JoshuaSeidel/tank-monitor/boards/allinone-freenove.yaml

# ALL-IN-ONE -- Freenove ESP32-S3-WROOM (FNK0085; ESP32-S3-WROOM-1 N8R8,
# DevKitC-1 pin layout). The whole 75 gal on one board: two heaters, the fan,
# both temperature probes, TDS, pH, the floor leak sensor, lux and spectral,
# and the Chihiros light itself over BLE (packages/light_wrgb2.yaml).
# No light pod, no ADS1115, no separate light bridge, and every device on its
# own GPIOs.
#
# CUTTING OVER FROM THE OLD LIGHT BRIDGE: the lamp takes one BLE connection
# at a time. Power the aquarium-light-bridge ESP32 OFF before this board
# comes up, or the two fight for the lamp. Then turn off Home Assistant's
# "Aquarium 75 - apply light phase" automation -- this board owns the phase
# now ("Light Phase" select) and HA only reports it.
#
# Successor to boards/xiao-esp32s3-lg-dual.yaml + the light pod. Everything
# the controller did is carried over unchanged -- the tank controller, the
# dual-heater lockstep, the gradient split, tank mode, the leak alarm, the
# BLE v3 link to the panel. What changed is only where each signal enters:
#
#   - pH, TDS and leak read on the chip's own ADC1, one pin each. The
#     ADS1115 is gone because the S3 has exactly TWO I2C controllers
#     (ESPHome refuses a third bus on this chip) and both are spent on the
#     light sensors, one each.
#   - Lux and spectral are read here, directly. The pod's BLE push and the
#     controller's "rx_" globals are no longer in the path.
#
# RECALIBRATE pH and TDS after the swap, and re-check the leak thresholds:
# every analog value now comes through a different converter.
#
# ---------------------------------------------------------------------
# PIN MAP -- Freenove ESP32-S3-WROOM (labels are GPIO numbers on this board)
# ---------------------------------------------------------------------
#   signal                       GPIO   notes
#   pH board signal (blue)       1      ADC1_CH0
#   DS18B20 A (control probe)    4      4.7k pull-up to 3V3 (CAM_SIOD)
#   DS18B20 B (cross-check)      5      4.7k pull-up to 3V3 (CAM_SIOC)
#   TDS board signal             6      ADC1_CH5
#   Leak sensor                  7      ADC1_CH6; 2.2M + 100nF to GND at the pin
#   Heater A relay               8
#   Heater B relay               9
#   Fan relay                    10
#   BH1750 SDA / SCL             15 / 16   I2C bus "bus_lux"
#   AS7341 SDA / SCL             17 / 18   I2C bus "bus_spec"
#
# Left alone on purpose:
#   0, 3, 45, 46   strapping pins -- a sensor holding one at a level at
#                  reset can stop the board booting
#   35, 36, 37     the octal PSRAM
#   19, 20         native USB
#   43, 44         the USB-serial console
#   38, 39, 40     the microSD slot
#   2, 48          onboard LED and WS2812 RGB LED
# GPIO 4-18 also run to the (unfitted) camera connector; do not fit one.
# GPIO4 and GPIO5 are the camera's SCCB bus (CAM_SIOD / CAM_SIOC) and are
# PULLED UP TO 3V3 ON THE BOARD, camera or not. Never put an analog input
# on them: on 2026-09-28 TDS (GPIO4) sat at ~2.33 V in air with the probe
# unplugged, and the leak input (GPIO5) read a dead-flat 3.15 V -- "wet" --
# against its 2.2M pull-down from the first boot. The 1-Wire buses live
# there instead, because 1-Wire wants a pull-up anyway: the board's sits in
# parallel with the 4.7k.
#
# ---------------------------------------------------------------------
# POWER -- the one thing that is still shared
# ---------------------------------------------------------------------
# One 3V3 pin and one GND pin (bottom right, beside GPIO19 -- NOT the
# DevKitC-1 positions) for seven things that need 3.3 V. Splice off
# the board, as on every board in this project.
#
# The light sensors are on long leads up to the fixture, and on 2026-09-17
# a shorted BH1750 lead browned out the 3V3 rail of the board driving the
# heaters. Separate I2C buses stop a dead sensor from holding the OTHER
# sensor's lines (which is exactly what the dead BH1750 did on the pod), but
# a short on a sensor's POWER lead still pulls the whole rail down. Feed the
# two light sensors from their own small 3.3 V regulator off the 5V pin, or
# through a resettable fuse, so a sensor fault cannot brown out the heaters.
#
# WHAT THIS FILE OWES THE SHARED PACKAGES -- the board contract:
#   one_wire bus onewire_a       -> dallas_temp in packages/sensors.yaml
#   sensor id: tds_voltage       -> packages/sensors.yaml
#   sensor id: ph_voltage        -> packages/ph.yaml
#   sensor id: tank_lux          -> packages/control.yaml (illuminance)
#   output id: heater_output     -> packages/control.yaml
#   output id: fan_output        -> packages/control.yaml
#   substitution spectral_i2c    -> packages/spectral.yaml
#   substitution light_mac       -> packages/light_wrgb2.yaml
#   water_temp_b, temp_gradient, grad_ema_*  -> packages/ble_link_v3.yaml

substitutions:
  side_a_name: "A"
  side_b_name: "B"
  # Leak thresholds, volts. Carried over from the ADS1115 build; the
  # internal ADC reads the same node slightly differently, so check wet and
  # dry against "Leak Sensor Voltage" before trusting the alarm.
  leak_on_v:  "1.2"
  leak_off_v: "0.8"
  spectral_i2c: bus_spec
  # The 75's lamp -- a WRGB II Pro 120. It advertises as
  # "DYWPR120E9B8ED2E998E": the name carries its own address, so check any
  # new value against the name. Random-static; the tracker learns the type
  # from the advertisement. Read off Home Assistant's Bluetooth adapter on
  # 2026-09-29. Load-critical, so it lives here in the versioned board file
  # rather than a wrapper.
  # The CF:20:3B:6D:17:C1 this held until then is the upstream author's own
  # DYNT90, copied from the fork's example defaults -- never this tank's
  # lamp. ble_client only connects after hearing its exact address, so with
  # it the board waited silently for a lamp that is not in the house.
  light_mac: "E9:B8:ED:2E:99:8E"
  # Where the follow-the-sun light phases take sunrise and sunset from:
  # south-central Pennsylvania, rounded to ~10 km.
  light_latitude: "39.8"
  light_longitude: "-76.7"

esp32:
  board: esp32-s3-devkitc-1
  variant: esp32s3
  flash_size: 8MB
  framework:
    type: esp-idf

# MAC-based unique_ids, as on every board here: the legacy generator omits
# the device name, and same-named entities on two boards collide.
mqtt:
  discovery_unique_id_generator: mac
  # NETWORK OUTAGES MUST NOT STOP THE HEATER LOOP.
  #
  # 2026-09-30 11:01 the router went down for ~4 minutes. This board's last
  # MQTT message was 11:00:06; it rebooted at 11:02:06 on the TASK WATCHDOG
  # (uptime 185 s at 11:05:11), i.e. the main loop -- the loop that runs the
  # heaters -- stopped for over 5 s about a minute into the outage. Broker
  # restarts (TCP refused at once) never did this; a 15 s router stall on
  # 2026-10-06 did not either. The publish path that can block for 10 s is
  # closed for every board in packages/base.yaml (idf_send_async). What is
  # specific to this board is below and in the wifi block after it.
  #
  # keepalive 60 s: the default 15 s ended the session on every short
  # router stall (2026-10-06 02:49, "connection closed by client"), which
  # then re-sends every entity's discovery and state in one burst. 60 s rides
  # out a stall of under a minute; the broker marks the board offline after
  # 90 s of real silence instead of ~22. Kept to this board on purpose:
  # every other board keeps ESPHome's default, so how fast Home Assistant
  # sees them go offline is unchanged.
  keepalive: 60s

# The fallback access point (packages/base.yaml) starts after 90 s without
# Wi-Fi by default. It switches the radio to AP+STA on channel 1 and brings
# up the captive portal -- on a radio that is also holding two BLE links --
# and while the portal is up ESPHome stops scanning for the home network.
# The 2026-09-30 watchdog reset landed 60-120 s into the outage, squarely on
# that 90 s mark. Whether or not the AP start itself was the block, nothing
# good comes of it on a board bolted to a tank with known credentials: a
# router reboot is never 10 minutes, a credentials change is. Recovery by AP
# still works -- it just waits until the network is really gone. (Wi-Fi's own
# reboot_timeout, 15 min, is left alone: the AP is up from 10 to 15 min, the
# board reboots at 15 with its relays seeded off, and regulation resumes
# within seconds; the cycle repeats only while the network stays down.)
wifi:
  ap:
    ap_timeout: 10min

# Two 1-Wire buses, one probe each: a flooded probe takes down its own bus
# and nothing else, and sensors.yaml's address-less probe drops in unmodified
# (it is bound to bus A by the !extend below).
one_wire:
  - platform: gpio
    id: onewire_a
    pin: GPIO4      # control probe. 4.7k pull-up to 3V3 (+ the board's CAM_SIOD pull-up).
  - platform: gpio
    id: onewire_b
    pin: GPIO5      # cross-check probe. 4.7k pull-up to 3V3 (+ the board's CAM_SIOC pull-up).

# Two buses, one sensor each. 10 kHz on both: the leads run up to the
# fixture, and the slow clock buys capacitance margin on a long run.
i2c:
  - id: bus_lux
    sda: GPIO15
    scl: GPIO16
    frequency: 10kHz
    scan: true
  - id: bus_spec
    sda: GPIO17
    scl: GPIO18
    frequency: 10kHz
    scan: true

# Bus autopsy, run BEFORE the I2C driver claims the pins (bus priority is
# 1000; this is 1001). With the chip's own pull-ups off it asks each line:
# does a powered sensor's pull-up reach it (ext-pullup), and is it tied hard
# to 3V3 (drives-low)? Reported through "I2C Devices". List form: a mapping
# on_boot in a package can be dropped when packages merge.
esphome:
  on_boot:
    - priority: -200
      then:
        - script.execute: apply_mode
    # The per-side relays are published only from slow_pwm's
    # state_change_action, so with the tank at temperature (duty 0, no edge)
    # they sat at "unknown" indefinitely. control.yaml seeds heater_relay and
    # fan_relay the same way; slow_pwm is off at boot, so false is the truth.
    - priority: -100
      then:
        - binary_sensor.template.publish:
            id: heater_a_relay
            state: false
        - binary_sensor.template.publish:
            id: heater_b_relay
            state: false
    - priority: 1001
      then:
        - lambda: |-
            const gpio_num_t pins[4] = {GPIO_NUM_15, GPIO_NUM_16, GPIO_NUM_17, GPIO_NUM_18};
            const char *names[4] = {"lux SDA", "lux SCL", "spec SDA", "spec SCL"};
            std::string r;
            for (int i = 0; i < 4; i++) {
              gpio_config_t c{};
              c.pin_bit_mask = 1ULL << pins[i];
              c.mode = GPIO_MODE_INPUT;
              c.pull_up_en = GPIO_PULLUP_DISABLE;
              c.pull_down_en = GPIO_PULLDOWN_ENABLE;
              c.intr_type = GPIO_INTR_DISABLE;
              gpio_config(&c);
              delayMicroseconds(200);
              const int ext = gpio_get_level(pins[i]);
              c.mode = GPIO_MODE_INPUT_OUTPUT_OD;
              c.pull_up_en = GPIO_PULLUP_ENABLE;
              c.pull_down_en = GPIO_PULLDOWN_DISABLE;
              gpio_config(&c);
              gpio_set_level(pins[i], 0);
              delayMicroseconds(200);
              const int low = gpio_get_level(pins[i]);
              gpio_set_level(pins[i], 1);
              delayMicroseconds(200);
              char b[72];
              snprintf(b, sizeof(b), "%s%s ext-pullup %s, drives-low %s",
                       i ? "; " : "", names[i], ext ? "yes" : "NO", low == 0 ? "yes" : "NO");
              r += b;
            }
            id(i2c_autopsy) = r;
            ESP_LOGI("i2c", "autopsy: %s", r.c_str());

# The cross-check probe below is also the controller's veto: if the two
# probes disagree by more than the band for five minutes the heater goes
# off (control.yaml's "Probes Disagree"). Distinct from "Probe Disagreement"
# further down, which is the instantaneous gradient against its own
# threshold -- that one tells you about the tank, this one stops the heater.
tank_controller:
  cross_check: water_temp_b
  # Eight degrees, not control.yaml's two. On a 48" tank the two probes sit
  # 40" apart with a heater beside each; a real gradient of a degree or
  # two is a MEASUREMENT here (see "Temperature Gradient"), not a fault.
  # The veto exists for a probe that is lying -- the flooded DS18B20 of
  # 2026-09-14 read half the water temperature, 35 degF off -- and 8 degF
  # catches that with room to spare while never firing on the tank itself.
  # First-boot default only: the controller persists the band, and the
  # "Probe Disagreement Band" entity (raised to 15 below) changes it live.
  disagreement_band: 8.0
  # Hard high cutout raised for cycling. control.yaml's 82 degF sits above
  # anything the 70-80 slider allows but BELOW a cycling target, and the
  # setpoint is clamped to the cutout. 88 degF is still nowhere near what
  # troubles glass, silicone or a Jager; it is a backstop on the water,
  # not a limit on the target.
  max_temperature: 88.0


sensor:
  # Bind the shared package's probe to bus A, and name both probes by side.
  - id: !extend water_temp
    one_wire_id: onewire_a
  - id: !extend water_temp_f
    name: "Water Temperature ${side_a_name}"

  # ---------------------------------------------------------------
  # Analog: pH, TDS, leak -- the chip's own ADC1, one pin each
  # ---------------------------------------------------------------
  # 12 dB attenuation covers 0-~3.1 V: the TDS board swings to ~2.3 V and
  # the pH board to ~3.0 V. 16 conversions averaged per reading, then a
  # median, because the radio's transmit bursts land on the supply as
  # short spikes. Two-point calibration through this same ADC (ph.yaml's
  # capture buttons, sensors.yaml's TDS calibration) cancels its offset
  # and gain error; recalibrate both after moving to this board.
  - platform: adc
    pin: GPIO6
    id: tds_voltage
    attenuation: 12db
    samples: 16
    update_interval: 500ms
    internal: true
    filters:
      - median:
          window_size: 20
          send_every: 20
          send_first_at: 20

  - platform: adc
    pin: GPIO1
    id: ph_voltage
    attenuation: 12db
    samples: 16
    update_interval: 1s
    internal: true
    filters:
      - median:
          window_size: 10
          send_every: 5
          send_first_at: 5

  # Floor leak sensor (Level Sense LS-2600): open when dry, ~1.4 MOhm and
  # SOURCING when wet, so the input wants a pull-DOWN. At the pin:
  #   red   -> 3V3            2.2M  between GPIO7 and GND
  #   black -> GPIO7          100nF between GPIO7 and GND
  # Dry reads 0 V, wet ~1-2.5 V. The 100nF is not optional: a megohm node
  # on six feet of cable is an antenna, and it is also what gives the ADC's
  # sampling capacitor a stiff source to charge from.
  - platform: adc
    pin: GPIO7
    id: leak_voltage
    name: "Leak Sensor Voltage"
    unit_of_measurement: "V"
    accuracy_decimals: 2
    entity_category: diagnostic
    attenuation: 12db
    samples: 16
    update_interval: 2s
    filters:
      - median:
          window_size: 5
          send_every: 5
          send_first_at: 3

  # ---------------------------------------------------------------
  # Lux -- the BH1750 on its own bus, read here, no pod in the path
  # ---------------------------------------------------------------
  # sensors.yaml's BH1750 would land on an ambiguous bus (there are two), so
  # it is removed and re-declared on bus_lux as the RAW reading. tank_lux --
  # what control.yaml's thermal model consumes -- is the daylight-corrected
  # figure below, exactly as the controller computed it from the pod.
  - id: !remove tank_lux
  - platform: bh1750
    name: "Tank Light Level Raw"
    id: lux_raw
    i2c_id: bus_lux
    address: 0x23
    update_interval: 30s
    accuracy_decimals: 0
    entity_category: diagnostic
    filters:
      - filter_out: nan

  # The lamp emits essentially no near-infrared and daylight is full of it,
  # so NIR/clear (packages/spectral.yaml's sp_nir_ratio) says how much of
  # the lux is the sun. Linear unmix against the learned daylight reference
  # (cal_nir_ref, in packages/ble_link_v3.yaml): 0 NIR = all fixture, the
  # reference = all sun. Fails OPEN: no reference yet, or no spectral
  # reading, passes lux through unchanged rather than zeroing the model's
  # light term.
  - platform: template
    name: "Tank Light Level"
    id: tank_lux
    unit_of_measurement: lx
    device_class: illuminance
    state_class: measurement
    accuracy_decimals: 0
    update_interval: 30s
    lambda: |-
      const float lux = id(lux_raw).state;
      if (isnan(lux)) return {};
      const float ref = id(cal_nir_ref);
      const float nir = id(sp_nir_ratio).state;
      if (ref <= 0.0f || isnan(nir)) return lux;
      float frac = 1.0f - (nir / ref);
      if (frac < 0.0f) frac = 0.0f;
      if (frac > 1.0f) frac = 1.0f;
      return lux * frac;

  # Learn the daylight reference from every spectral reading. Fixture light
  # only ever DILUTES NIR/clear, so the running maximum is the purest
  # daylight sample there is. Only above 50 lux (in the dark both channels
  # are near zero and the ratio is noise), decaying on a ~16 day half-life so
  # it follows the seasons. Same rule the controller applied to pod frames;
  # the decay factor is scaled for one reading a minute, same as before.
  - id: !extend sp_nir_ratio
    on_value:
      then:
        - lambda: |-
            const float lux = id(lux_raw).state;
            if (isnan(x) || isnan(lux) || lux <= 50.0f) return;
            if (x > id(cal_nir_ref)) id(cal_nir_ref) = x;
            else id(cal_nir_ref) *= 0.99997f;

  # ---------------------------------------------------------------
  # Cross-check temperature probe
  # ---------------------------------------------------------------
  # NOT a second control input. packages/control.yaml regulates on
  # water_temp alone, and that is deliberate: two independent loops on one
  # body of water mislearn each other's heat as ambient bias.
  #
  # This probe exists to answer two questions the control probe cannot:
  # "is the control probe still telling the truth" and "does this tank
  # actually have a gradient".
  - platform: dallas_temp
    one_wire_id: onewire_b
    internal: true
    id: water_temp_b
    update_interval: 10s
    accuracy_decimals: 2
    filters:
      # No filter_out: nan. A stale cross-check reading is worse than none
      # -- it would keep agreeing with a control probe that has died.
      - median:
          window_size: 5
          send_every: 1
          send_first_at: 1
      # Probe B gets its OWN offset. A DS18B20 is +/-0.5 degC absolute and
      # the control loop holds +/-0.3 degF, so two uncalibrated probes can
      # read nearly a degree apart in identical water. Cross-calibrate both
      # in the same cup before trusting any gradient number below.
      - lambda: return x + id(cal_temp_offset_b_c);

  - platform: template
    name: "Water Temperature ${side_b_name}"
    unit_of_measurement: "°F"
    device_class: temperature
    state_class: measurement
    accuracy_decimals: 2
    update_interval: 30s
    lambda: |-
      if (std::isnan(id(water_temp_b).state)) return {};
      return id(water_temp_b).state * 9.0f / 5.0f + 32.0f;

  # SIGNED gradient, side A minus side B. Positive means the A half is
  # warmer. The sign is the actionable half of this number -- absolute value
  # tells you a gradient exists, the sign tells you which end to aim
  # circulation at. That matters here because the canister draws from one
  # side, so the two halves are not hydraulically equivalent even with
  # identical heat going into each.
  #
  # Log this for a week before believing in a hot spot: under ~0.3 degF
  # there is nothing to chase (and you cannot resolve less than that with
  # two DS18B20 anyway), over ~1 degF you have a circulation problem that
  # more heaters would mask rather than fix.
  - platform: template
    name: "Temperature Gradient"
    id: temp_gradient
    unit_of_measurement: "°F"
    icon: "mdi:thermometer-lines"
    state_class: measurement
    accuracy_decimals: 2
    update_interval: 30s
    lambda: |-
      const float a = id(water_temp).state;
      const float b = id(water_temp_b).state;
      if (std::isnan(a) || std::isnan(b)) return {};
      return (a - b) * 9.0f / 5.0f;

  # ---------------------------------------------------------------
  # Splitting the gradient by cause
  # ---------------------------------------------------------------
  # A gradient that appears ONLY while the heaters run is a mixing problem:
  # heat is not leaving the end it is injected at. A gradient that persists
  # while they are idle is an ambient problem: one end of the tank is losing
  # heat to a cold wall, window or floor. Those have completely different
  # fixes, and the raw gradient cannot tell them apart.
  #
  # With both elements on the same duty, the heating figure is also the
  # heater-failure detector. If one element dies or its relay stops closing,
  # its half stops receiving heat and this number walks away from zero and
  # stays there while the idle figure does not.
  - platform: template
    name: "Gradient While Heating"
    unit_of_measurement: "°F"
    icon: "mdi:thermometer-lines"
    entity_category: diagnostic
    accuracy_decimals: 2
    update_interval: 60s
    lambda: |-
      // Expire rather than publish stale. If the tank has not been in this
      // regime recently the honest answer is "unavailable", not a figure
      // from last week presented as current -- the same reasoning that
      // keeps filter_out: nan off the probe in packages/sensors.yaml.
      const uint32_t t = id(grad_heating_ms);
      if (t == 0) return {};
      if (millis() - t > 21600000UL) return {};
      if (std::isnan(id(grad_ema_heating))) return {};
      return id(grad_ema_heating);

  - platform: template
    name: "Gradient While Idle"
    unit_of_measurement: "°F"
    icon: "mdi:thermometer-lines"
    entity_category: diagnostic
    accuracy_decimals: 2
    update_interval: 60s
    lambda: |-
      const uint32_t t = id(grad_idle_ms);
      if (t == 0) return {};
      if (millis() - t > 21600000UL) return {};
      if (std::isnan(id(grad_ema_idle))) return {};
      return id(grad_ema_idle);

binary_sensor:
  # Per-element contact state. control.yaml's "Heater" is the pair; these
  # are the individual relays, and seeing them out of lockstep means a relay
  # is not following its drive.
  - platform: template
    trigger_on_initial_state: true
    id: heater_a_relay
    name: "Heater ${side_a_name}"
    device_class: running
    icon: "mdi:radiator"

  - platform: template
    trigger_on_initial_state: true
    id: heater_b_relay
    name: "Heater ${side_b_name}"
    device_class: running
    icon: "mdi:radiator"

  # Fires when the probes disagree by more than the configured band. That is
  # either a real gradient, a dead heater, or a probe drifting out of
  # calibration -- all three are things you want to be told about rather
  # than discover in the data months later.
  - platform: template
    trigger_on_initial_state: true
    name: "Probe Disagreement"
    id: probe_disagreement
    device_class: problem
    entity_category: diagnostic
    lambda: |-
      if (std::isnan(id(temp_gradient).state)) return {};
      return fabsf(id(temp_gradient).state) > id(cal_gradient_alarm_f);

  # Wet = the sensor sources into the pull-down = the voltage rises. Two
  # thresholds (substitutions above): above leak_on_v is wet, below
  # leak_off_v is dry, and in between the answer is "whatever it was" --
  # returning an empty optional leaves the state alone. That band is what
  # stops a floor that reads 0.4 V on a humid night from flickering the
  # alarm; a 0.5 V single threshold did exactly that on 2026-09-17.
  #
  # The delays are the debounce on top. A splash that bridges the tabs for
  # a few seconds is not a leak; a leak does not un-bridge them in ten.
  - platform: template
    # trigger_on_initial_state: ESPHome defaults it OFF, and then a binary
    # sensor's FIRST state fires no callbacks -- MQTT only sends a state that
    # already exists when it connects. This one's first state lands ~16 s
    # after boot (first ADC median + the 10 s delayed_off), after MQTT is up,
    # so a dry floor was never sent and HA kept the last firmware's "wet"
    # (2026-09-28). Every published template binary sensor in this repo sets
    # it, so none can go silent this way; none has on_state automations.
    trigger_on_initial_state: true
    name: "Leak"
    id: leak_floor
    device_class: moisture
    lambda: |-
      const float v = id(leak_voltage).state;
      if (std::isnan(v)) return {};
      if (v > ${leak_on_v}f) return true;
      if (v < ${leak_off_v}f) return false;
      return {};
    filters:
      - delayed_on: 5s
      - delayed_off: 10s

# ---------------------------------------------------------------
# Heaters: ONE loop, TWO relays, BOTH heating together
# ---------------------------------------------------------------
# Equal duty to both elements, simultaneously, always. NOT staged.
#
# Staging (A carries low demand alone, B joins above a threshold) delivers
# heat more smoothly in TIME -- 150W pulsing instead of 300W. That is the
# wrong trade for this tank, because it necessarily puts all the low-demand
# heat into one half. The canister draws from a single side, so flow is
# already directional; stacking a heat asymmetry on top of a flow asymmetry
# manufactures exactly the gradient the second probe exists to detect.
#
# Even injection wins. The 300W-vs-150W pulse difference is invisible
# against a thermal time constant measured in hours. The gradient it would
# create is not.
#
# packages/control.yaml takes a single `heater:` FloatOutput and its RLS
# model carries exactly one heater term (phi = [heater, fan, T-TREF, light,
# 1]). heater_output satisfies that contract and the pair behaves as one
# 300W actuator whose combined gain the model learns as a unit.
#
# The two relays stay separate rather than being ganged onto one GPIO: it
# costs a pin this board has plenty of, and it keeps the ability to cut one
# element independently if a relay welds or an element fails.
output:
  - platform: slow_pwm
    id: heater_a_pwm
    pin: GPIO8
    period: 900s
    # False is already the ESPHome default (verified in slow_pwm/output.py,
    # 2026.8.2) -- stated explicitly because it matters more here than
    # anywhere else in this repo: it keeps the two windows PHASE-LOCKED. They start together at boot and
    # are always written in the same lambda below, so equal duty means both
    # elements are energised over the same part of each window. Letting the
    # cycles restart independently would drift them apart and, at partial
    # duty, alternate the halves -- reintroducing precisely the side-to-side
    # asymmetry this design exists to avoid.
    restart_cycle_on_state_change: false
    # packages/control.yaml defines heater_relay and fan_relay but does NOT
    # publish them -- its comment says outright they are "published from
    # slow_pwm's state_change_action in the board file". Without these the
    # entities sit at the false seeded on_boot forever, and Home Assistant
    # shows a heater that never runs while the tank regulates perfectly.
    state_change_action:
      - lambda: id(heater_a_closed) = state;
      - binary_sensor.template.publish:
          id: heater_relay
          # OR, not AND: this entity answers "is heat being delivered". A
          # failed element is not its job -- Gradient While Heating covers
          # that, and the per-side sensors below show the pair in lockstep.
          state: !lambda "return id(heater_a_closed) || id(heater_b_closed);"
      - binary_sensor.template.publish:
          id: heater_a_relay
          state: !lambda "return state;"

  - platform: slow_pwm
    id: heater_b_pwm
    pin: GPIO9
    period: 900s
    restart_cycle_on_state_change: false
    state_change_action:
      - lambda: id(heater_b_closed) = state;
      - binary_sensor.template.publish:
          id: heater_relay
          state: !lambda "return id(heater_a_closed) || id(heater_b_closed);"
      - binary_sensor.template.publish:
          id: heater_b_relay
          state: !lambda "return state;"

  # NOT inverted. The D-1585TL relay outlet module is active-high -- apply
  # voltage to the control terminal and the relay closes. The cheap bare
  # boards are active-low; this is not one of those, and `inverted: true`
  # here would run every duty cycle exactly backwards.
  - platform: slow_pwm
    id: fan_output
    pin: GPIO10
    period: 900s
    restart_cycle_on_state_change: false
    state_change_action:
      - binary_sensor.template.publish:
          id: fan_relay
          state: !lambda "return state;"

  - platform: template
    id: heater_output
    type: float
    write_action:
      - lambda: |-
          const float d = clamp(state, 0.0f, 1.0f);
          // From nothing to something -- Filling released, or a call for
          // heat after coasting -- closes the relays NOW. slow_pwm decides
          // at the start of each 900 s window whether the contacts close,
          // so a demand that arrives mid-window would otherwise wait out
          // the rest of it: up to fifteen minutes of "heating" with both
          // relays open. Only this edge restarts the window. A duty that
          // merely changes mid-window keeps its place in it, because
          // restarting on every 30 s adjustment would hold the contacts
          // closed for as long as the duty kept creeping up.
          if (id(heater_demand) <= 0.0f && d > 0.0f) {
            id(heater_a_pwm).restart_cycle();
            id(heater_b_pwm).restart_cycle();
          }
          id(heater_demand) = d;
          // Same duty, same instant, both halves of the tank. If these ever
          // diverge in effect, the gradient sensors above are what tell you.
          id(heater_a_pwm).set_level(d);
          id(heater_b_pwm).set_level(d);

interval:
  # Gradient accumulation. 30s matches the probes' publish cadence; k=0.01
  # is roughly a 50 minute time constant, which is short against the tank's
  # thermal time constant of hours but long enough to reject probe noise.
  - interval: 30s
    then:
      - lambda: |-
          const float a = id(water_temp).state;
          const float b = id(water_temp_b).state;
          if (std::isnan(a) || std::isnan(b)) return;
          const float g = (a - b) * 9.0f / 5.0f;
          const float k = 0.01f;

          // Three-way, not two. "demand > 0" would bin a 2% duty cycle --
          // 18 seconds of contact per 15 minute window -- as heating, and
          // dilute the heating average with what is effectively idle data.
          // Samples in the ambiguous middle are DISCARDED rather than
          // forced into a bin they would corrupt.
          const float d = id(heater_demand);
          if (d >= 0.05f) {
            float &e = id(grad_ema_heating);
            e = std::isnan(e) ? g : (k * g + (1.0f - k) * e);
            id(grad_heating_ms) = millis();
          } else if (d <= 0.0f) {
            float &e = id(grad_ema_idle);
            e = std::isnan(e) ? g : (k * g + (1.0f - k) * e);
            id(grad_idle_ms) = millis();
          }

# ---------------------------------------------------------------
# Tank mode: Normal / Filling / Cycling
# ---------------------------------------------------------------
# Three things a new tank is, in order. The controller does the work
# (set_hold, set_setpoint_override); this is the switch on the wall.
#
#   Filling   Every output held off and nothing judged. Probes in air read
#             room temperature and disagree; a Jager out of water must not
#             be powered; the learner must not watch any of it. Releasing
#             the hold re-anchors the model and caps heat while it settles,
#             because it is new water.
#   Cycling   Regulates on "Cycling Target" instead of "Target Temperature"
#             without touching it, so the owner's number is still there when
#             the tank is done. Everything else -- fan, learning, faults --
#             runs as normal.
#   Normal    The setpoint entity, as on every other board.
select:
  - platform: template
    name: "Tank Mode"
    id: tank_mode_select
    icon: "mdi:fishbowl-outline"
    entity_category: config
    options: ["Normal", "Filling", "Cycling"]
    # Reads the global back rather than keeping its own copy -- one owner,
    # same reason the setpoint number reads the controller.
    lambda: |-
      switch (id(tank_mode)) {
        case 1: return {"Filling"};
        case 2: return {"Cycling"};
        default: return {"Normal"};
      }
    update_interval: 30s
    set_action:
      - lambda: |-
          id(tank_mode) = (x == "Filling") ? 1 : (x == "Cycling") ? 2 : 0;
      - script.execute: apply_mode

script:
  - id: apply_mode
    mode: restart
    then:
      - lambda: |-
          // A restored Filling is a Filling nobody is standing at.
          if (id(tank_mode) == 1 && millis() < 15000) id(tank_mode) = 0;
          const int m = id(tank_mode);
          id(controller).set_hold(m == 1);
          id(controller).set_setpoint_override(
              m == 2 ? (id(cycling_target_f) - 32.0f) * 5.0f / 9.0f : NAN);
          id(tank_mode_select).publish_state(m == 1 ? "Filling" : m == 2 ? "Cycling" : "Normal");

globals:
  # Result of the boot-time bus autopsy (see esphome: on_boot above).
  - id: i2c_autopsy
    type: std::string
    restore_value: false
    initial_value: '""'
  # Mirrors the demand handed to heater_output so the gradient metrics can
  # tell heating from idle. Not restored: it is a live value, and a stale
  # one after reboot would mis-bin the first sample.
  - id: heater_demand
    type: float
    restore_value: false
    initial_value: '0.0'

  # Gradient EMAs. Restored, because these are long-baseline averages and
  # throwing them away on every OTA would restart the diagnosis from zero.
  - id: grad_ema_heating
    type: float
    restore_value: true
    initial_value: 'NAN'
  - id: grad_ema_idle
    type: float
    restore_value: true
    initial_value: 'NAN'

  # Freshness stamps for the two EMAs. NOT restored: millis() restarts at
  # zero on boot, so a restored timestamp would be meaningless. Zero means
  # "no sample in this boot yet", which reads as unavailable -- honest,
  # because a restored average has no provenance in the current session.
  - id: grad_heating_ms
    type: uint32_t
    restore_value: false
    initial_value: '0'
  - id: grad_idle_ms
    type: uint32_t
    restore_value: false
    initial_value: '0'

  # Live contact state, so either relay's action can publish the pair's OR.
  - id: heater_a_closed
    type: bool
    restore_value: false
    initial_value: 'false'
  - id: heater_b_closed
    type: bool
    restore_value: false
    initial_value: 'false'

  - id: cal_temp_offset_b_c
    type: float
    restore_value: true
    initial_value: '0.0'
  - id: cal_gradient_alarm_f
    type: float
    restore_value: true
    initial_value: '1.0'

  # Cycling target, degF. 82: nitrifying bacteria double fastest in the low
  # 80s, and 82 is the top of what an empty tank's equipment shrugs at.
  - id: cycling_target_f
    type: float
    restore_value: true
    initial_value: '82.0'
  # 0 normal, 1 filling, 2 cycling. Restored, so a reboot mid-cycle stays
  # warm. Filling is NOT restored: apply_mode maps a restored 1 back to
  # normal, because a controller that reboots with its outputs held off
  # and nobody at the tank is a cold tank by morning.
  - id: tank_mode
    type: int
    restore_value: true
    initial_value: '0'

number:
  # The veto band's ceiling. control.yaml caps the entity at 5 degF, which
  # is right for a one-probe board and wrong for this one -- see the
  # disagreement_band comment on the controller above.
  - id: !extend probe_disagreement_band
    max_value: 15.0
  # Same reason as the probe's name: two offsets, two names.
  - id: !extend cal_temp_offset_num
    name: "Cal Temp Offset ${side_a_name}"

  - platform: template
    name: "Cycling Target"
    id: cycling_target_num
    icon: "mdi:bacteria-outline"
    entity_category: config
    unit_of_measurement: "°F"
    device_class: temperature
    min_value: 78.0
    max_value: 86.0
    step: 0.5
    update_interval: 60s
    lambda: "return id(cycling_target_f);"
    set_action:
      - lambda: id(cycling_target_f) = x;
      # Each of these views republishes as soon as it is set, not at the
      # next poll -- see packages/sensors.yaml.
      - component.update: cycling_target_num
      - script.execute: apply_mode

  - platform: template
    name: "Cal Temp Offset ${side_b_name}"
    id: cal_temp_offset_b_num
    icon: "mdi:thermometer-plus"
    entity_category: config
    min_value: -5.0
    max_value: 5.0
    step: 0.1
    unit_of_measurement: "°F"
    update_interval: 60s
    # Celsius on the inside like every other temperature in this project,
    # Fahrenheit on the face because that is what a human reads.
    lambda: "return id(cal_temp_offset_b_c) * 9.0f / 5.0f;"
    set_action:
      - lambda: id(cal_temp_offset_b_c) = x * 5.0f / 9.0f;
      - component.update: cal_temp_offset_b_num

  - platform: template
    name: "Gradient Alarm Threshold"
    id: cal_gradient_alarm_num
    icon: "mdi:thermometer-alert"
    entity_category: config
    min_value: 0.1
    max_value: 5.0
    step: 0.1
    unit_of_measurement: "°F"
    update_interval: 60s
    lambda: "return id(cal_gradient_alarm_f);"
    set_action:
      - lambda: id(cal_gradient_alarm_f) = x;
      - component.update: cal_gradient_alarm_num

text_sensor:
  # BUILD GUARD -- see boards/xiao-esp32s3.yaml for the incident this exists
  # because of. id(ble_tx) is defined ONLY in packages/ble_link.yaml, so
  # building this board without that file fails at compile rather than
  # producing a controller that runs the tank perfectly and advertises
  # nothing for the panel to connect to.
  - platform: template
    name: "Link Payload"
    icon: "mdi:code-string"
    entity_category: diagnostic
    update_interval: 60s
    lambda: 'return {id(ble_tx)};'

  # Which light sensor answers, on which bus, every minute -- the sensor
  # components only probe at boot and then sit at "unknown". A TIMEOUT is a
  # HUNG bus (a device or wire holding SDA/SCL), not a missing device: it is
  # reported and nothing more is sent to that bus this round, because each
  # further transaction waits out the same ~100 ms and a sweep of them would
  # trip the task watchdog. On "no ack" the bus is swept, so a sensor at the
  # wrong address shows up where it is. The boot autopsy is appended on any
  # failure.
  - platform: template
    name: "I2C Devices"
    id: i2c_devices
    icon: "mdi:transit-connection-variant"
    entity_category: diagnostic
    update_interval: 60s
    lambda: |-
      std::string out;
      bool any_bad = false;
      auto check = [&](i2c::I2CBus *bus, uint8_t addr, const char *label) {
        App.feed_wdt();
        const auto err = bus->write_readv(addr, nullptr, 0, nullptr, 0);
        if (!out.empty()) out += ", ";
        out += label;
        if (err == i2c::ERROR_OK) { out += " ok"; return; }
        any_bad = true;
        if (err == i2c::ERROR_TIMEOUT) { out += " BUS STUCK"; return; }
        out += (err == i2c::ERROR_NOT_ACKNOWLEDGED) ? " no ack" : " error";
        std::string found;
        for (uint8_t a = 0x08; a < 0x78; a++) {
          App.feed_wdt();
          const auto e = bus->write_readv(a, nullptr, 0, nullptr, 0);
          if (e == i2c::ERROR_TIMEOUT) { found += " (hung mid-sweep)"; break; }
          if (e != i2c::ERROR_OK) continue;
          char b[8];
          snprintf(b, sizeof(b), " 0x%02X", a);
          found += b;
        }
        out += found.empty() ? " (bus empty)" : " (bus has" + found + ")";
      };
      check(id(bus_lux), 0x23, "BH1750");
      check(id(bus_spec), 0x39, "AS7341");
      if (any_bad && !id(i2c_autopsy).empty()) out += "; at boot: " + id(i2c_autopsy);
      return out;

  # WHY IT LAST CRASHED -- kept across the reboot and across power cuts
  # (components/crash_report). "Reset Reason" says only "task watchdog";
  # these say where. "Last Crash" is the reason, the core, and for a
  # watchdog the unit of work the main loop was stuck in and for how long,
  # e.g. "Task wdt on core 0; main loop stuck 5.0 s in 'mqtt' ...".
  # "Last Crash Backtrace" is the PC and backtrace; decode against the
  # firmware.elf of the build that crashed:
  #   xtensa-esp32s3-elf-addr2line -pfiaC -e .esphome/build/<name>/build/<name>.elf 0x... 0x...
  # Both read "none recorded" until there is something to record.
  - platform: template
    name: "Last Crash"
    icon: "mdi:alert-octagon-outline"
    entity_category: diagnostic
    update_interval: 60s
    lambda: 'return {id(crash).summary()};'
  - platform: template
    name: "Last Crash Backtrace"
    icon: "mdi:format-list-numbered"
    entity_category: diagnostic
    update_interval: 60s
    lambda: 'return {id(crash).backtrace()};'

button:
  # Once a crash has been read and dealt with, so the next one is not
  # confused with it.
  - platform: template
    name: "Clear Crash Report"
    icon: "mdi:delete-sweep-outline"
    entity_category: config
    on_press:
      - lambda: id(crash).clear();

# The crash record itself: ESPHome's panic backtrace plus a task-watchdog
# breadcrumb, captured at boot and saved to flash. See the text sensors above.
external_components:
  - source:
      type: git
      url: https://github.com/JoshuaSeidel/tank-monitor
      ref: main
    components: [crash_report]
    refresh: 0s

crash_report:
  id: crash

# The AS7341 and its derived values (shares, NIR ratio, saturation), shared
# with the light pod. Included from HERE so this board file alone is a
# complete build: a wrapper cannot leave the spectral side out.
packages:
  spectral: !include ../packages/spectral.yaml
  # The lamp, held over BLE, with the phase table and lux-based detection on
  # this chip. Needs tank_lux above (lamp-only lux) and the esp32_ble block
  # from ble_link_v3.yaml. Included here for the same reason: a wrapper
  # cannot leave it out.
  light: !include ../packages/light_wrgb2.yaml
