JoshuaSeidel/tank-monitor/packages/light_wrgb2.yaml

# The tank light, driven from the tank's own board.
#
# A Chihiros WRGB II / WRGB II Pro, controlled over BLE from the same chip
# that runs the heaters, using the protocol helpers in the
# JoshuaSeidel/chihiros-esphome fork. This replaces the separate
# aquarium-light-bridge ESP32 AND the Home Assistant automation that used to
# re-push the schedule every half hour. Everything here runs on the board:
# Home Assistant only reports it, exactly as it does for the heaters.
#
# TUNING NEEDS NO FLASH. The phase table is stored in flash memory, not
# compiled in: "Light White/Red/Green/Blue/Ramp/On Time/Off Time" edit the
# selected phase, save it, and push it within a couple of seconds. The
# numbers in light_seed_defaults are first-boot defaults and what "Reset
# Light Phase to Defaults" restores -- nothing else.
#
# Needs from the including build:
#   ${light_mac}      the lamp's BLE MAC (the board file sets it)
#   sensor tank_lux   LAMP-ONLY lux -- daylight already unmixed out by NIR
#   global cal_nir_ref  the learned daylight reference (ble_link_v3.yaml)
#   time sntp_time    packages/base.yaml
#   esp32_ble         packages/ble_link_v3.yaml (the panel server)
#   ble_guard         packages/ble_link_v3.yaml (disconnect reasons)
#
# ---------------------------------------------------------------------
# WHY THE LINK IS HELD OPEN
# ---------------------------------------------------------------------
# The upstream bridge connects, pushes, and disconnects, and scans
# continuously so it can reconnect at any moment. On a board that also runs
# the heaters and serves the panel, a scanner that never stops is radio time
# taken from Wi-Fi and the panel link for no reason. Here the tracker scans
# from boot only until the lamp connects, then stops; it scans again only if
# the link drops. With both links up, the radio does not scan at all.
#
# Held open, the link also means the Chihiros app CANNOT connect -- the lamp
# takes one connection at a time. That is the point: nothing overrides the
# phase selected here. "Release Light for App" hands the lamp over for 30
# minutes and then takes it back, re-pushing the selected phase, so whatever
# was done in the app is undone automatically. A release cannot be left on.
#
# ---------------------------------------------------------------------
# DETECTION -- "the schedule says lit and the lamp is dark"
# ---------------------------------------------------------------------
# The lamp cannot report its state, so this looks at it instead. tank_lux is
# lamp-only light (daylight is removed by its near-infrared signature, see
# the board file), so it answers "is the fixture actually on" even with the
# window open. Room LEDs have no NIR either and DO leak into it, which is why
# the lit level is LEARNED rather than guessed -- a guessed lux threshold was
# wrong on this project for a year once already:
#
#   * During the plateau of a lit phase, while the reading looks lit, the
#     plateau lux is tracked as an average ("Light Learned Lux").
#   * Plateau and reading below max(20 lx, a quarter of the learned level)
#     for 5 minutes = the lamp is dark when it should be lit. Re-push.
#   * Well outside the photoperiod and reading above HALF the learned level
#     for 5 minutes = lit when it should be dark (lights left on overnight is
#     the algae case). Re-push. Disabled until BOTH a lit level and the
#     daylight reference (cal_nir_ref) have been learned: tank_lux passes
#     sunlight through as lamp light until then, so a fresh board on a sunny
#     afternoon would otherwise "detect" a lamp that is actually off.
#   * No more than one fix per 15 minutes; after 3 fixes that did not take,
#     stop pushing and raise "Light Not Responding" rather than hammering the
#     radio. It clears the moment the lamp matches again.
#
# Ramps are excluded (5 min margin each side on top of the ramp itself) --
# mid-ramp the lux is legitimately anywhere. Assumes the photoperiod does
# not cross midnight; none of the phases do.

substitutions:
  # The Nordic UART service every Chihiros device speaks. Fixed by the
  # lamp, not a setting. The panel server in ble_link_v3.yaml advertises the
  # same service UUID -- no clash: that is the board's own GATT server, this
  # is a client connection to a different device.
  light_ble_service: "6e400001-b5a3-f393-e0a9-e50e24dcca9e"
  light_ble_tx:      "6e400002-b5a3-f393-e0a9-e50e24dcca9e"
  light_ble_rx:      "6e400003-b5a3-f393-e0a9-e50e24dcca9e"
  # "true" for a WRGB II Pro (independent white channel).
  light_pro: "true"

external_components:
  - source:
      type: git
      url: https://github.com/JoshuaSeidel/chihiros-esphome
      ref: main
    components: [chihiros_ble]
    # The default 1d would silently build yesterday's protocol code.
    refresh: 0s

# Pulls in the protocol headers (frame builder, WRGB2Device). No options.
chihiros_ble:

# Scans from boot until the lamp is found; the ble_client's on_connect stops
# it. Same timing the upstream bridge uses; active, because the lamp's name
# rides in the scan response.
esp32_ble_tracker:
  scan_parameters:
    active: true
    interval: 320ms
    window: 60ms
    continuous: true

ble_client:
  - mac_address: ${light_mac}
    id: light_ble
    on_connect:
      then:
        - lambda: |-
            id(light_linked) = true;
            id(light_up_ms) = millis();
        - esp32_ble_tracker.stop_scan:
        - logger.log:
            level: INFO
            format: "light: linked, scanning stopped"
        # Always re-push on (re)connect: whatever happened while the link was
        # down -- a reboot, a release to the app -- is overwritten here.
        - delay: 500ms
        - script.execute: light_push
    # Fires on ESP_GATTC_CLOSE_EVT only. ESPHome has two ways to end a link
    # WITHOUT that event: its 10 s "Timeout waiting for CLOSE_EVT, forcing
    # IDLE" path in BLEClientBase::loop(), and a BLE stack teardown. Either
    # one left Light Linked stuck on and the scan never restarted -- the
    # watchdog interval below is what catches those.
    on_disconnect:
      then:
        - script.execute:
            id: light_link_down
            cause: 1

globals:
  - id: light_device
    type: chihiros::WRGB2Device
    restore_value: false
  - id: light_linked
    type: bool
    restore_value: false
    initial_value: 'false'
  - id: light_released
    type: bool
    restore_value: false
    initial_value: 'false'
  # Link diagnostics. Not restored: they describe this boot's link, and
  # millis() stamps mean nothing after a reboot. "Light Link Drops" is
  # total_increasing, so Home Assistant handles the reset to 0.
  #   light_down_cause  0 none yet, 1 disconnect event, 2 found by watchdog
  - id: light_link_drops
    type: uint32_t
    restore_value: false
    initial_value: '0'
  - id: light_up_ms
    type: uint32_t
    restore_value: false
    initial_value: '0'
  - id: light_down_cause
    type: int
    restore_value: false
    initial_value: '0'
  # Consecutive 10 s watchdog checks that disagreed with the real client
  # state / found the scan not running. Two in a row before acting, so a
  # transition caught mid-flight is not "corrected".
  - id: light_wd_strikes
    type: int
    restore_value: false
    initial_value: '0'
  - id: light_scan_strikes
    type: int
    restore_value: false
    initial_value: '0'
  # The selected phase, resolved from the table in light_select_phase.
  # Detection compares the lamp against THIS, not against what was last
  # successfully pushed.
  - id: lp_valid
    type: bool
    restore_value: false
    initial_value: 'false'
  - id: lp_auto
    type: bool
    restore_value: false
    initial_value: 'false'
  - id: lp_on_min
    type: int
    restore_value: false
    initial_value: '540'
  - id: lp_off_min
    type: int
    restore_value: false
    initial_value: '840'
  - id: lp_ramp
    type: int
    restore_value: false
    initial_value: '30'
  - id: lp_r
    type: int
    restore_value: false
    initial_value: '0'
  - id: lp_g
    type: int
    restore_value: false
    initial_value: '0'
  - id: lp_b
    type: int
    restore_value: false
    initial_value: '0'
  - id: lp_w
    type: int
    restore_value: false
    initial_value: '0'
  # Learned plateau lux. Persisted: a reboot should not forget what "on"
  # looks like. Zeroed on a phase change, because the new phase is a
  # different brightness.
  - id: light_learned_lux
    type: float
    restore_value: true
    initial_value: '0.0'
  - id: light_mismatch_min
    type: int
    restore_value: false
    initial_value: '0'
  - id: light_fix_attempts
    type: int
    restore_value: false
    initial_value: '0'
  - id: light_last_fix_ms
    type: uint32_t
    restore_value: false
    initial_value: '0'
  - id: light_not_responding
    type: bool
    restore_value: false
    initial_value: 'false'
  # 0 unknown, 1 off phase, 2 dark (outside the photoperiod), 3 ramping,
  # 4 lit (plateau). Drives detection and "Light Expected".
  - id: light_expected
    type: int
    restore_value: false
    initial_value: '0'
  # THE PHASE TABLE, stored in flash so it is tuned from Home Assistant or the
  # board's own page and survives reboots and reflashes -- changing a
  # brightness never needs a build. Five phases x seven fields, in select
  # order: [on_min, off_min, ramp, W, R, G, B]. Zero until first boot seeds
  # it from light_seed_defaults, which is the ONLY place default values are
  # written down.
  - id: light_table
    type: std::array<int, 35>
    restore_value: true
  - id: light_table_seeded
    type: bool
    restore_value: true
    initial_value: 'false'
  # FOLLOW THE SUN, per phase, in select order. 0 = the table's fixed times.
  # >0 = the lights span today's sunrise to sunset and this many minutes of
  # it are full brightness; the rest of the natural day is a slow dawn and
  # dusk ramp. Kept apart from light_table so adding it did not discard the
  # stored table. Seeded by light_seed_sun, the only place its defaults live.
  - id: light_sun_plateau
    type: std::array<int, 5>
    restore_value: true
  - id: light_sun_seeded
    type: bool
    restore_value: true
    initial_value: 'false'
  # The selected phase follows the sun: lp_on/off/ramp are computed, not
  # read from the table. lp_sun_day is the day of year they were computed
  # for (-1 = not yet), so the minute tick recomputes after midnight and
  # once the clock first syncs.
  - id: lp_sun
    type: bool
    restore_value: false
    initial_value: 'false'
  - id: lp_sun_day
    type: int
    restore_value: false
    initial_value: '-1'

# Sunrise/sunset are computed here, from the clock, so a sun-following phase
# keeps working with Home Assistant down. The tank is in south-central
# Pennsylvania; one decimal (~10 km) is well under a minute of sunrise.
# Override light_latitude/light_longitude in the board file if it moves.
sun:
  id: light_sun
  time_id: sntp_time
  latitude: ${light_latitude}
  longitude: ${light_longitude}

# List form: a mapping on_boot in a package can be dropped when packages
# merge. Late priority, so the select has already restored its option. This
# only resolves the phase; the push itself happens on connect.
esphome:
  on_boot:
    - priority: -100
      then:
        - if:
            condition:
              lambda: return !id(light_table_seeded);
            then:
              - script.execute:
                  id: light_seed_defaults
                  only: -1
              - script.wait: light_seed_defaults
        # Boards seeded before follow-the-sun existed have a table but no
        # sun settings; give them the defaults without touching the table.
        - if:
            condition:
              lambda: return !id(light_sun_seeded);
            then:
              - script.execute:
                  id: light_seed_sun
                  only: -1
              - script.wait: light_seed_sun
        - script.execute: light_select_phase

select:
  - platform: template
    name: "Light Phase"
    id: light_phase
    icon: mdi:weather-sunny
    optimistic: true
    restore_value: true
    initial_option: "Phase 1 - Plants in"
    options:
      - "Off (cycling)"
      - "Phase 1 - Plants in"
      - "Phase 2 - Shrimp"
      - "Phase 3 - Fish"
      - "Phase 4 - Mature"
    on_value:
      then:
        - script.execute: light_select_phase
        - lambda: |-
            // New phase, new brightness: what "lit" looked like before no
            // longer applies. Detection falls back to the 20 lx floor for
            // "should be lit" and stays off for "should be dark" until the
            // next plateau relearns it.
            id(light_learned_lux) = 0.0f;
            id(light_mismatch_min) = 0;
            id(light_fix_attempts) = 0;
            id(light_not_responding) = false;
        - script.execute: light_refresh_controls
        - script.execute: light_push

script:
  # DEFAULTS -- the one place default values are written down. Times in
  # minutes since midnight; W is the dimming lever, R/G/B track it at
  # roughly 0.8 / 0.45 / 0.3. Sized for PAR at the substrate of the 75
  # (lamp on its stock legs, ~46 cm of water), estimated from a PAR sweep
  # of a WRGB II Pro 90 (Chihiros publishes none), so +/-30%:
  #   Phase 1 ~32-37  bottom of the 30-50 band for a fertilised, no-CO2 tank
  #   Phase 2 ~40-50  the no-CO2 ceiling; past ~50-60 algae outgrows plants
  #   Phase 3 ~55-65  CO2 on (hold here 1-2 weeks while CO2 settles)
  #   Phase 4 ~75-90  CO2 dialled in; what the red stems want
  # The previous ladder (W25..W45) put the substrate at ~16-37, i.e. the
  # old ceiling was the bottom of the right band. Writes every phase (only: -1) on first boot, or just
  # one phase for "Reset Light Phase to Defaults". After that the stored
  # table (light_table) is the truth and these numbers are never read.
  - id: light_seed_defaults
    parameters:
      only: int
    then:
      - lambda: |-
          static const int defaults[35] = {
            540, 840, 30,  0,  0,  0,  0,   // Off (cycling)
            540, 960, 45, 45, 36, 20, 14,   // Phase 1 - Plants in
            540, 960, 45, 55, 45, 28, 20,   // Phase 2 - Shrimp
            540, 990, 45, 60, 50, 32, 24,   // Phase 3 - Fish
            540, 990, 45, 70, 60, 38, 30,   // Phase 4 - Mature
          };
          for (int ph = 0; ph < 5; ph++) {
            if (only != -1 && ph != only) continue;
            for (int f = 0; f < 7; f++) id(light_table)[ph * 7 + f] = defaults[ph * 7 + f];
          }
          id(light_table_seeded) = true;
          ESP_LOGI("light", "phase defaults written (%s)", only < 0 ? "all" : "one phase");
      - script.execute:
          id: light_seed_sun
          only: !lambda return only;
      - script.wait: light_seed_sun

  # Follow-the-sun defaults: Phases 3 and 4 (CO2 on) span sunrise to sunset
  # with 7 h and 7.5 h at full brightness. Past ~8 h of full light a planted
  # tank feeds algae whatever the season, so the natural day's length goes
  # into the dawn and dusk ramps rather than into the plateau. Phases 1-2
  # keep fixed hours: they run while the tank is new and light-limited.
  - id: light_seed_sun
    parameters:
      only: int
    then:
      - lambda: |-
          static const int sun_defaults[5] = {0, 0, 0, 420, 450};
          for (int ph = 0; ph < 5; ph++) {
            if (only != -1 && ph != only) continue;
            id(light_sun_plateau)[ph] = sun_defaults[ph];
          }
          id(light_sun_seeded) = true;

  # Resolve the selected phase from the stored table into lp_*. "Off
  # (cycling)" is manual mode at 0 whatever its stored values say: the lamp
  # stays dark regardless of its clock.
  - id: light_select_phase
    then:
      - lambda: |-
          auto idx = id(light_phase).active_index();
          if (!idx.has_value() || *idx >= 5) {
            id(lp_valid) = false;
            ESP_LOGW("light", "no valid phase selected; nothing will be pushed");
            return;
          }
          const int ph = (int) *idx, b = ph * 7;
          auto &t = id(light_table);
          auto clampi = [](int v, int lo, int hi) { return v < lo ? lo : (v > hi ? hi : v); };
          id(lp_auto) = ph != 0;
          id(lp_on_min) = clampi(t[b + 0], 0, 1439);
          id(lp_off_min) = clampi(t[b + 1], 0, 1439);
          id(lp_ramp) = clampi(t[b + 2], 0, 150);
          id(lp_w) = ph ? clampi(t[b + 3], 0, 100) : 0;
          id(lp_r) = ph ? clampi(t[b + 4], 0, 100) : 0;
          id(lp_g) = ph ? clampi(t[b + 5], 0, 100) : 0;
          id(lp_b) = ph ? clampi(t[b + 6], 0, 100) : 0;
          id(lp_valid) = true;

          // Follow the sun: lights span sunrise..sunset; the plateau is
          // capped and the rest of the day becomes ramp. Ramps are limited
          // to 150 min (the lamp's range here), so on a long summer day the
          // span is trimmed symmetrically around solar noon. Without a valid
          // clock or a computable sun the table's fixed times stand in.
          id(lp_sun) = false;
          const int plat = ph ? id(light_sun_plateau)[ph] : 0;
          auto now = id(sntp_time).now();
          if (plat > 0) {
            id(lp_sun_day) = now.is_valid() ? now.day_of_year : -1;
            auto rise = id(light_sun).sunrise(-0.833);
            auto set = id(light_sun).sunset(-0.833);
            if (now.is_valid() && rise.has_value() && set.has_value()) {
              // Next events, in UTC; the lamp runs local wall-clock time.
              auto r = ESPTime::from_epoch_local(rise->timestamp);
              auto z = ESPTime::from_epoch_local(set->timestamp);
              int on = r.hour * 60 + r.minute, off = z.hour * 60 + z.minute;
              const int day = off - on;
              if (day > 60) {
                int ramp = (day - plat) / 2;
                if (ramp > 150) {
                  const int noon = (on + off) / 2, span = plat + 2 * 150;
                  on = noon - span / 2;
                  off = on + span;
                  ramp = 150;
                } else if (ramp < 15) {
                  ramp = 15;       // a short winter day shortens the plateau
                }
                id(lp_on_min) = clampi(on, 0, 1439);
                id(lp_off_min) = clampi(off, 0, 1439);
                id(lp_ramp) = ramp;
                id(lp_sun) = true;
              }
            }
            if (!id(lp_sun))
              ESP_LOGW("light", "phase %d follows the sun but sunrise is not computable yet; fixed times until it is", ph);
          }
          ESP_LOGI("light", "phase %d: %s%s %02d:%02d-%02d:%02d ramp %d W%d R%d G%d B%d",
                   ph, ph ? "auto" : "manual-off", id(lp_sun) ? " (sun)" : "",
                   id(lp_on_min) / 60, id(lp_on_min) % 60,
                   id(lp_off_min) / 60, id(lp_off_min) % 60,
                   id(lp_ramp), id(lp_w), id(lp_r), id(lp_g), id(lp_b));

  # The seven controls read the ACTIVE phase's slot; after a phase change
  # they are told to re-read at once rather than waiting for their poll.
  - id: light_refresh_controls
    then:
      - component.update: light_ctl_white
      - component.update: light_ctl_red
      - component.update: light_ctl_green
      - component.update: light_ctl_blue
      - component.update: light_ctl_ramp
      - component.update: light_ctl_on
      - component.update: light_ctl_off
      - component.update: light_ctl_sun_hours

  # A control was changed. Debounced, so dragging a slider sends one push
  # when it settles rather than one per step; restart, so the last value
  # wins.
  - id: light_changed
    mode: restart
    then:
      - delay: 1500ms
      - script.execute: light_select_phase
      - script.execute: light_refresh_controls
      - script.execute: light_push

  # Send the selected phase to the lamp. restart: the newest request wins,
  # so any number of rapid phase changes ends on the last one picked --
  # prepare() clears whatever was still queued from the interrupted run.
  - id: light_push
    mode: restart
    then:
      - if:
          condition:
            lambda: return !id(lp_valid);
          then:
            - script.execute: light_select_phase
      - if:
          condition:
            lambda: return id(light_linked) && id(lp_valid);
          then:
            - lambda: |-
                const bool pro = ${light_pro};
                id(light_device).prepare(
                  id(sntp_time).now(), id(lp_auto),
                  id(lp_on_min) / 60, id(lp_on_min) % 60,
                  id(lp_off_min) / 60, id(lp_off_min) % 60,
                  (uint8_t) id(lp_ramp),
                  (uint8_t) id(lp_r), (uint8_t) id(lp_g), (uint8_t) id(lp_b),
                  pro ? (uint8_t) id(lp_w) : chihiros::data::SKIP);
            - while:
                condition:
                  lambda: return id(light_linked) && id(light_device).has_next();
                then:
                  - ble_client.ble_write:
                      id: light_ble
                      service_uuid: ${light_ble_service}
                      characteristic_uuid: ${light_ble_tx}
                      value: !lambda return id(light_device).next();
                  - delay: 200ms
            - logger.log:
                level: INFO
                format: "light: phase pushed"
          else:
            - logger.log:
                level: INFO
                format: "light: not linked; the phase goes out on connect"

  # The link is down, however that was found out. One place, so the
  # disconnect event and the watchdog cannot disagree about what "down"
  # does: clear Light Linked, count the drop (not when the lamp was handed
  # to the app on purpose), and scan to reconnect unless released.
  - id: light_link_down
    mode: queued
    parameters:
      cause: int
    then:
      - lambda: |-
          if (id(light_linked) && !id(light_released)) {
            id(light_link_drops)++;
            id(light_down_cause) = cause;
          }
          id(light_linked) = false;
      - if:
          condition:
            lambda: return !id(light_released);
          then:
            - logger.log:
                level: WARN
                format: "light: link lost (%s), scanning to reconnect"
                args: ['cause == 2 ? "found by watchdog" : "disconnect event"']
            - esp32_ble_tracker.start_scan:
                continuous: true

  # Hand the lamp to the Chihiros app for 30 minutes, then take it back.
  # restart: pressing again extends the window rather than stacking.
  - id: light_release
    mode: restart
    then:
      - globals.set:
          id: light_released
          value: 'true'
      - esp32_ble_tracker.stop_scan:
      - switch.turn_off: light_link
      - logger.log:
          level: INFO
          format: "light: released to the app for 30 min"
      - delay: 30min
      - globals.set:
          id: light_released
          value: 'false'
      - switch.turn_on: light_link
      - esp32_ble_tracker.start_scan:
          continuous: true
      - logger.log:
          level: INFO
          format: "light: taken back; the phase is re-pushed on connect"

switch:
  # Enables/disables the client. On = hold the link. Only light_release
  # turns it off, and only for a bounded time.
  - platform: ble_client
    ble_client_id: light_ble
    id: light_link
    internal: true
    restore_mode: ALWAYS_ON

interval:
  # LINK WATCHDOG. Light Linked is set and cleared by the client's connect
  # and close events, and both can be missed (see on_disconnect above). This
  # compares it with the client's real state every 10 s and fixes whichever
  # way it is wrong, then checks that an unlinked lamp is actually being
  # scanned for -- the scan is what reconnects it, and nothing else restarts
  # a scan that has stopped.
  - interval: 10s
    then:
      - lambda: |-
          using esphome::esp32_ble_tracker::ClientState;
          using esphome::esp32_ble_tracker::ScannerState;
          if (id(light_released)) {           // handed to the app on purpose
            id(light_wd_strikes) = 0;
            id(light_scan_strikes) = 0;
            return;
          }
          const bool real = id(light_ble).connected();
          if (id(light_linked) != real) {
            if (++id(light_wd_strikes) < 2) return;
            id(light_wd_strikes) = 0;
            if (!real) {
              ESP_LOGW("light", "watchdog: Light Linked was on but the client is %s -- its disconnect was never "
                       "reported; clearing it and scanning", esphome::esp32_ble_tracker::client_state_to_string(id(light_ble).state()));
              id(light_link_down).execute(2);
            } else {
              ESP_LOGW("light", "watchdog: the client is connected but Light Linked was off -- its connect was "
                       "never reported; setting it and pushing the phase");
              id(light_linked) = true;
              id(light_up_ms) = millis();
              id(light_push).execute();
            }
            return;
          }
          id(light_wd_strikes) = 0;
          // Unlinked, idle, and nobody scanning: the lamp can never come back.
          auto *trk = esphome::esp32_ble_tracker::global_esp32_ble_tracker;
          if (!real && trk != nullptr && id(light_ble).state() == ClientState::IDLE &&
              trk->get_scanner_state() == ScannerState::IDLE) {
            if (++id(light_scan_strikes) < 2) return;
            id(light_scan_strikes) = 0;
            ESP_LOGW("light", "watchdog: lamp unlinked and no scan running; restarting the scan");
            trk->set_scan_continuous(true);
            trk->start_scan();
          } else {
            id(light_scan_strikes) = 0;
          }

  - interval: 1min
    then:
      - lambda: |-
          auto now = id(sntp_time).now();
          if (!now.is_valid() || !id(lp_valid)) { id(light_expected) = 0; return; }
          const int m = now.hour * 60 + now.minute;

          // Daily clock resync at 03:00, while the lamp is dark anyway, so
          // its RTC never drifts off the schedule's edges.
          if (now.hour == 3 && now.minute == 0) id(light_push).execute();

          // A sun-following phase moves every day: recompute after midnight
          // (and once the clock first syncs) and push while the lamp is dark.
          {
            auto i = id(light_phase).active_index();
            if (i.has_value() && *i > 0 && *i < 5 && id(light_sun_plateau)[*i] > 0 &&
                id(lp_sun_day) != now.day_of_year) {
              id(light_select_phase).execute();
              id(light_refresh_controls).execute();
              id(light_push).execute();
              return;
            }
          }

          const int on = id(lp_on_min), off = id(lp_off_min), ramp = id(lp_ramp);
          int expect;
          if (!id(lp_auto)) expect = 1;                                         // off phase
          else if (m >= on + ramp + 5 && m < off - ramp - 5) expect = 4;        // plateau
          else if (m >= on - 5 && m < off + 5) expect = 3;                      // ramping
          else expect = 2;                                                      // dark
          id(light_expected) = expect;

          // Nothing to judge while the lamp is handed to the app, while the
          // link is down (that is its own alarm), or without a lux reading.
          const float lux = id(tank_lux).state;
          if (id(light_released) || !id(light_linked) || std::isnan(lux)) {
            id(light_mismatch_min) = 0;
            return;
          }

          float &learned = id(light_learned_lux);
          bool mismatch = false;
          if (expect == 4) {
            const float dark_below = std::max(20.0f, 0.25f * learned);
            if (lux < dark_below) {
              mismatch = true;
            } else if (learned <= 0.0f) {
              learned = lux;                                   // first plateau sample
            } else {
              learned += 0.05f * (lux - learned);              // ~20 min average
            }
          } else if (expect == 1 || expect == 2) {
            // Needs the daylight reference too. tank_lux fails OPEN -- until
            // cal_nir_ref is learned, sunlight passes through as if it were
            // the lamp, and a bright afternoon outside the photoperiod would
            // read as "lamp left on" and end in a false Not Responding.
            if (learned > 0.0f && id(cal_nir_ref) > 0.0f && lux > 0.5f * learned)
              mismatch = true;
          }

          if (!mismatch) {
            if (id(light_not_responding))
              ESP_LOGI("light", "lamp matches the schedule again");
            id(light_mismatch_min) = 0;
            id(light_fix_attempts) = 0;
            id(light_not_responding) = false;
            return;
          }

          id(light_mismatch_min)++;
          ESP_LOGW("light", "lamp does not match: expected %s, lamp lux %.0f, learned %.0f (%d min)",
                   expect == 4 ? "lit" : "dark", lux, learned, id(light_mismatch_min));
          if (id(light_mismatch_min) < 5 || id(light_not_responding)) return;
          if (id(light_last_fix_ms) != 0 && millis() - id(light_last_fix_ms) < 15UL * 60UL * 1000UL) return;

          if (id(light_fix_attempts) >= 3) {
            id(light_not_responding) = true;
            ESP_LOGE("light", "3 re-pushes did not fix it; stopping until the lamp matches again");
            return;
          }
          id(light_fix_attempts)++;
          id(light_last_fix_ms) = millis();
          ESP_LOGW("light", "re-pushing the phase (attempt %d of 3)", id(light_fix_attempts));
          id(light_push).execute();

# THE CONTROLS -- a window onto the ACTIVE phase's slot in light_table.
# Change one and that phase is saved (flash, survives reboot and reflash)
# and pushed to the lamp; pick another phase and they show its values. The
# repo pattern for stored values: update_interval + lambda + set_action, the
# global owns the value, the entity is only a view of it. "Off (cycling)" is
# always manual-off; editing its slot has no effect on the lamp.
number:
  - platform: template
    name: "Light White"
    id: light_ctl_white
    icon: mdi:white-balance-sunny
    unit_of_measurement: "%"
    min_value: 0
    max_value: 100
    step: 1
    mode: box
    update_interval: 60s
    lambda: |-
      auto i = id(light_phase).active_index();
      if (!i.has_value() || *i >= 5) return {};
      return (float) id(light_table)[*i * 7 + 3];
    set_action:
      - lambda: |-
          auto i = id(light_phase).active_index();
          if (!i.has_value() || *i >= 5) return;
          id(light_table)[*i * 7 + 3] = (int) x;
          id(light_learned_lux) = 0.0f;   // new brightness: relearn what lit looks like
      - script.execute: light_changed
  - platform: template
    name: "Light Red"
    id: light_ctl_red
    icon: mdi:alpha-r-circle
    unit_of_measurement: "%"
    min_value: 0
    max_value: 100
    step: 1
    mode: box
    update_interval: 60s
    lambda: |-
      auto i = id(light_phase).active_index();
      if (!i.has_value() || *i >= 5) return {};
      return (float) id(light_table)[*i * 7 + 4];
    set_action:
      - lambda: |-
          auto i = id(light_phase).active_index();
          if (!i.has_value() || *i >= 5) return;
          id(light_table)[*i * 7 + 4] = (int) x;
          id(light_learned_lux) = 0.0f;   // new brightness: relearn what lit looks like
      - script.execute: light_changed
  - platform: template
    name: "Light Green"
    id: light_ctl_green
    icon: mdi:alpha-g-circle
    unit_of_measurement: "%"
    min_value: 0
    max_value: 100
    step: 1
    mode: box
    update_interval: 60s
    lambda: |-
      auto i = id(light_phase).active_index();
      if (!i.has_value() || *i >= 5) return {};
      return (float) id(light_table)[*i * 7 + 5];
    set_action:
      - lambda: |-
          auto i = id(light_phase).active_index();
          if (!i.has_value() || *i >= 5) return;
          id(light_table)[*i * 7 + 5] = (int) x;
          id(light_learned_lux) = 0.0f;   // new brightness: relearn what lit looks like
      - script.execute: light_changed
  - platform: template
    name: "Light Blue"
    id: light_ctl_blue
    icon: mdi:alpha-b-circle
    unit_of_measurement: "%"
    min_value: 0
    max_value: 100
    step: 1
    mode: box
    update_interval: 60s
    lambda: |-
      auto i = id(light_phase).active_index();
      if (!i.has_value() || *i >= 5) return {};
      return (float) id(light_table)[*i * 7 + 6];
    set_action:
      - lambda: |-
          auto i = id(light_phase).active_index();
          if (!i.has_value() || *i >= 5) return;
          id(light_table)[*i * 7 + 6] = (int) x;
          id(light_learned_lux) = 0.0f;   // new brightness: relearn what lit looks like
      - script.execute: light_changed
  - platform: template
    name: "Light Ramp"
    id: light_ctl_ramp
    icon: mdi:sun-angle
    unit_of_measurement: "min"
    min_value: 0
    max_value: 150
    step: 5
    mode: box
    update_interval: 60s
    lambda: |-
      auto i = id(light_phase).active_index();
      if (!i.has_value() || *i >= 5) return {};
      if (id(lp_sun)) return (float) id(lp_ramp);   // computed from the sun
      return (float) id(light_table)[*i * 7 + 2];
    set_action:
      - lambda: |-
          auto i = id(light_phase).active_index();
          if (!i.has_value() || *i >= 5) return;
          if (id(light_sun_plateau)[*i] > 0) {
            ESP_LOGW("light", "this phase follows the sun; its ramp is computed. Change Light Full Brightness Hours instead");
            id(light_ctl_ramp).publish_state(id(lp_ramp));
            return;
          }
          id(light_table)[*i * 7 + 2] = (int) x;
      - script.execute: light_changed

  # Follow-the-sun phases only: hours of full brightness inside today's
  # sunrise..sunset; the rest becomes dawn and dusk. 0 = fixed hours (the
  # On/Off Time and Ramp controls). Setting it on a phase turns following on.
  - platform: template
    name: "Light Full Brightness Hours"
    id: light_ctl_sun_hours
    icon: mdi:weather-sunny-alert
    unit_of_measurement: "h"
    min_value: 0
    max_value: 10
    step: 0.5
    mode: box
    update_interval: 60s
    lambda: |-
      auto i = id(light_phase).active_index();
      if (!i.has_value() || *i >= 5) return {};
      return id(light_sun_plateau)[*i] / 60.0f;
    set_action:
      - lambda: |-
          auto i = id(light_phase).active_index();
          if (!i.has_value() || *i == 0 || *i >= 5) return;
          id(light_sun_plateau)[*i] = (int) (x * 60.0f);
      - script.execute: light_changed

# Text, not datetime: ESPHome publishes a datetime over MQTT as JSON
# ({"hour":9,...}) and Home Assistant's MQTT time entity only accepts
# "HH:MM:SS" -- both directions failed, so the times sat at "unknown" in HA
# and could not be set from it. HH:MM text round-trips cleanly; anything
# else is refused on the device and the stored value republished.
text:
  - platform: template
    name: "Light On Time"
    id: light_ctl_on
    icon: mdi:weather-sunset-up
    mode: text
    min_length: 4
    max_length: 5
    pattern: "^([01]?[0-9]|2[0-3]):[0-5][0-9]$"
    update_interval: 60s
    lambda: |-
      auto i = id(light_phase).active_index();
      if (!i.has_value() || *i >= 5) return {};
      // Following the sun: show today's computed time, not the table's.
      const int v = id(lp_sun) ? id(lp_on_min) : id(light_table)[*i * 7 + 0];
      char buf[6];
      snprintf(buf, sizeof(buf), "%02d:%02d", v / 60, v % 60);
      return std::string(buf);
    set_action:
      - lambda: |-
          auto i = id(light_phase).active_index();
          if (!i.has_value() || *i >= 5) return;
          int h = -1, m = -1;
          if (sscanf(x.c_str(), "%d:%d", &h, &m) != 2 || h < 0 || h > 23 || m < 0 || m > 59) {
            ESP_LOGW("light", "Light On Time '%s' is not HH:MM; kept the stored value", x.c_str());
            id(light_ctl_on).publish_state(id(light_ctl_on).state);
            return;
          }
          if (id(light_sun_plateau)[*i] > 0) {
            ESP_LOGW("light", "this phase follows the sun; set Light Full Brightness Hours to 0 to use fixed times");
            id(light_ctl_on).publish_state(id(light_ctl_on).state);
            return;
          }
          id(light_table)[*i * 7 + 0] = h * 60 + m;
      - script.execute: light_changed
  - platform: template
    name: "Light Off Time"
    id: light_ctl_off
    icon: mdi:weather-sunset-down
    mode: text
    min_length: 4
    max_length: 5
    pattern: "^([01]?[0-9]|2[0-3]):[0-5][0-9]$"
    update_interval: 60s
    lambda: |-
      auto i = id(light_phase).active_index();
      if (!i.has_value() || *i >= 5) return {};
      // Following the sun: show today's computed time, not the table's.
      const int v = id(lp_sun) ? id(lp_off_min) : id(light_table)[*i * 7 + 1];
      char buf[6];
      snprintf(buf, sizeof(buf), "%02d:%02d", v / 60, v % 60);
      return std::string(buf);
    set_action:
      - lambda: |-
          auto i = id(light_phase).active_index();
          if (!i.has_value() || *i >= 5) return;
          int h = -1, m = -1;
          if (sscanf(x.c_str(), "%d:%d", &h, &m) != 2 || h < 0 || h > 23 || m < 0 || m > 59) {
            ESP_LOGW("light", "Light Off Time '%s' is not HH:MM; kept the stored value", x.c_str());
            id(light_ctl_off).publish_state(id(light_ctl_off).state);
            return;
          }
          if (id(light_sun_plateau)[*i] > 0) {
            ESP_LOGW("light", "this phase follows the sun; set Light Full Brightness Hours to 0 to use fixed times");
            id(light_ctl_off).publish_state(id(light_ctl_off).state);
            return;
          }
          id(light_table)[*i * 7 + 1] = h * 60 + m;
      - script.execute: light_changed

button:
  - platform: template
    name: "Release Light for App (30 min)"
    icon: mdi:cellphone-link
    on_press:
      - script.execute: light_release

  - platform: template
    name: "Push Light Phase Now"
    icon: mdi:clock-edit
    entity_category: diagnostic
    on_press:
      - script.execute: light_push

  - platform: template
    name: "Reset Light Phase to Defaults"
    icon: mdi:restore
    entity_category: config
    on_press:
      - script.execute:
          id: light_seed_defaults
          only: !lambda |-
            auto i = id(light_phase).active_index();
            return (i.has_value() && *i < 5) ? (int) *i : -2;
      - lambda: id(light_learned_lux) = 0.0f;
      - script.execute: light_changed

  - platform: template
    name: "Relearn Light Level"
    icon: mdi:refresh
    entity_category: config
    on_press:
      - lambda: |-
          ESP_LOGI("light", "learned lux cleared (was %.0f); relearning", id(light_learned_lux));
          id(light_learned_lux) = 0.0f;

binary_sensor:
  - platform: template
    trigger_on_initial_state: true
    name: "Light Linked"
    icon: mdi:bluetooth-connect
    device_class: connectivity
    entity_category: diagnostic
    lambda: return id(light_linked);

  - platform: template
    trigger_on_initial_state: true
    name: "Light Not Responding"
    device_class: problem
    lambda: return id(light_not_responding);

sensor:
  # Link health. Drops counts every unplanned loss of the lamp link (not a
  # release to the app); a steady climb with "supervision timeout" in Light
  # Link Last Drop is a radio-range problem, "peer closed it" is the lamp.
  - platform: template
    name: "Light Link Drops"
    icon: mdi:bluetooth-off
    entity_category: diagnostic
    state_class: total_increasing
    accuracy_decimals: 0
    update_interval: 60s
    lambda: return (float) id(light_link_drops);

  # Minutes since the link last came up; unknown while it is down.
  - platform: template
    name: "Light Link Uptime"
    icon: mdi:timer-outline
    entity_category: diagnostic
    unit_of_measurement: min
    device_class: duration
    accuracy_decimals: 0
    update_interval: 60s
    lambda: |-
      if (!id(light_linked)) return NAN;
      return (float) ((millis() - id(light_up_ms)) / 60000UL);

  - platform: template
    name: "Light Learned Lux"
    unit_of_measurement: lx
    icon: mdi:brightness-6
    accuracy_decimals: 0
    entity_category: diagnostic
    update_interval: 60s
    lambda: return id(light_learned_lux);

  # Whatever the lamp says back. Logged, not decoded: if the lamp turns out
  # to report its own state here, that is real readback and detection can
  # stop relying on lux alone.
  - platform: ble_client
    type: characteristic
    ble_client_id: light_ble
    service_uuid: ${light_ble_service}
    characteristic_uuid: ${light_ble_rx}
    id: light_notification
    notify: true
    internal: true
    lambda: |-
      ESP_LOGD("light", "notify (%d bytes): %s", (int) x.size(), chihiros::hex_dump(x).c_str());
      return NAN;

text_sensor:
  # Why the lamp link last ended: the radio's own disconnect reason, as the
  # board's GATT layer saw it (packages/ble_link_v3.yaml's ble_link_guard),
  # or that the disconnect was never reported and the watchdog found it.
  - platform: template
    name: "Light Link Last Drop"
    icon: mdi:bluetooth-off
    entity_category: diagnostic
    update_interval: 60s
    lambda: |-
      if (id(light_down_cause) == 0) return {"none since boot"};
      const int r = id(ble_guard).last_disconnect_reason(id(light_ble).get_address());
      char b[96];
      if (r < 0)
        snprintf(b, sizeof(b), "%s, no reason reported",
                 id(light_down_cause) == 2 ? "lost without an event (watchdog)" : "disconnected");
      else
        snprintf(b, sizeof(b), "%s%s (0x%02X)",
                 id(light_down_cause) == 2 ? "watchdog; last radio reason: " : "",
                 esphome::ble_link_guard::BLELinkGuard::reason_str(r), r);
      return {std::string(b)};

  - platform: template
    name: "Light Expected"
    icon: mdi:calendar-clock
    entity_category: diagnostic
    update_interval: 60s
    lambda: |-
      if (id(light_released)) return {"released to app"};
      if (!id(light_linked)) return {"no link"};
      switch (id(light_expected)) {
        case 1: return {"off phase"};
        case 2: return {"dark"};
        case 3: return {"ramping"};
        case 4: return {"lit"};
        default: return {"unknown"};
      }
