JoshuaSeidel/tank-monitor/packages/sensors.yaml

# Wet-side sensors, expressed without pins. The board package supplies the
# buses these sit on:
#   one_wire:  -> dallas_temp
#   i2c:       -> bh1750
#   an adc sensor with id: tds_voltage -> the TDS maths below
sensor:
  - platform: dallas_temp
    # Leave `address` off for a single probe; run once and copy the
    # address the log prints if you ever add a second one.
    # Internal and deliberately unnamed. It is the only Celsius value in
    # the project, so it is never published; the Fahrenheit sensor below
    # is the one Home Assistant sees, and that one owns the name. Two
    # entities called "Water Temperature" on one device would derive the
    # same MQTT object_id and collide.
    internal: true
    id: water_temp
    # 10s, not 2s. The control loop runs at 30s and the tank's time
    # constant is hours -- 2s sampling just multiplied the row count in
    # InfluxDB by 5x for no extra information.
    update_interval: 10s
    accuracy_decimals: 2
    filters:
      # No filter_out: nan here. Dropping failed reads means Home Assistant
      # keeps displaying the last good temperature forever after the probe
      # dies -- the device correctly showed PROBE FAULT while the dashboard
      # still read 72.6. A stale water temperature is worse than none.
      # NaN now propagates and the entity goes unavailable.
      - median:
          window_size: 5
          send_every: 1
          send_first_at: 1
      # Plausibility, AFTER the median so a single glitch is still absorbed
      # and only a sustained bogus value gets through to here. Two readings a
      # DS18B20 produces that are never a water temperature: exactly 0.0 C,
      # which is an all-zero bus read on a marginal data line -- and the CRC
      # of all zeros is zero, so it PASSES -- and 85.0 C, the power-on reset
      # value. On 2026-09-13, after the tank was moved, the probe returned a
      # clean 0.0 C for 25 minutes; the controller took it at face value as
      # an ice-cold tank and ran the heater at 100% into water that was
      # actually at 74.5 F. Converted to NaN, not dropped: a dropped sample
      # leaves the last good value in id(water_temp).state forever, which
      # is the stale-reading failure the comment above is about. NaN makes
      # the controller cut the heater after 120 s, the same as a dead probe.
      - lambda: |-
          if (x == 0.0f || x >= 85.0f) return NAN;
          return x;
      # Rate guard. The night after the two signatures above went in, the
      # same bus produced 11.8 C -- exactly half the tank, a one-bit slip --
      # which is a real temperature somewhere and passed everything. Water
      # in this tank moves ~3 degF per hour flat out, so a sample more than
      # 2 C from the last accepted one is not water. Twelve rejections in a
      # row (two minutes) re-anchor on the new value, so a genuine step
      # across a probe outage recovers instead of being refused forever;
      # by then the controller has already cut the heater on the NaNs.
      - lambda: |-
          static float last = NAN;
          static uint8_t rejected = 0;
          if (isnan(x)) return NAN;
          if (!isnan(last) && fabsf(x - last) > 2.0f && rejected < 12) {
            rejected++;
            return NAN;
          }
          rejected = 0;
          last = x;
          return x;
      # Calibration offset, applied HERE rather than on the published
      # Fahrenheit sensor: the controller reads this one, so correcting it
      # anywhere else would leave the control loop working from the
      # uncorrected value while the dashboard showed the corrected one.
      - lambda: return x + id(cal_temp_offset_c);

  - platform: template
    name: "TDS"
    id: tds
    unit_of_measurement: "ppm"
    icon: "mdi:water-opacity"
    accuracy_decimals: 0
    state_class: measurement
    update_interval: 30s
    lambda: |-
      const float v = id(tds_voltage).state;
      if (isnan(v)) return {};

      // Temperature-compensate to the 25 degC reference the probe's
      // polynomial is defined at. Fall back to 25 if the probe is absent.
      float t = id(water_temp).state;
      if (isnan(t)) t = 25.0f;
      const float coeff = 1.0f + 0.02f * (t - 25.0f);
      if (coeff <= 0.0f) return {};
      const float vc = v / coeff;

      // DFRobot/Keyestudio gravity TDS polynomial (V -> ppm), then the
      // 0.5 TDS-to-conductivity factor, then the user K-value.
      float ppm = (133.42f * vc * vc * vc
                   - 255.86f * vc * vc
                   + 857.39f * vc) * 0.5f * id(cal_tds_k);
      if (ppm < 0.0f) ppm = 0.0f;
      return ppm;
    filters:
      - clamp:
          min_value: 0
          max_value: 2000

  # The number to actually READ. A single sample from this probe is honest
  # about nothing: measured over a day of live data, the spread WITHIN one
  # hour had a median of 39 ppm and a maximum of 171 ppm -- larger than any
  # dose you would ever make. Two readings minutes apart can differ by more
  # than a water change does, which is how a 47 ppm "overnight rise" got
  # diagnosed here as a real event.
  #
  # 120 samples at 30s is a one-hour window, republished every minute.
  #
  # This is averaged HERE and not in Home Assistant, for exactly the reason
  # the calibration lives here: the remote panel over ESP-NOW and this
  # device's own web page must show the same trustworthy number with the
  # broker, the router and Home Assistant all down. A correction that only
  # exists in HA is a correction the tank does not have.
  - platform: template
    name: "TDS 1h Mean"
    id: tds_1h
    unit_of_measurement: "ppm"
    icon: "mdi:water-opacity"
    accuracy_decimals: 0
    state_class: measurement
    update_interval: 30s
    lambda: |-
      if (isnan(id(tds).state)) return {};
      return id(tds).state;
    filters:
      # send_first_at: 1 so a reboot republishes immediately on a partial
      # window rather than showing nothing for an hour. It converges.
      - sliding_window_moving_average:
          window_size: 120
          send_every: 2
          send_first_at: 1

  # Electrical conductivity, derived from the same reading
  - platform: template
    name: "Electrical Conductivity"
    unit_of_measurement: "µS/cm"
    icon: "mdi:flash"
    accuracy_decimals: 0
    state_class: measurement
    update_interval: 30s
    lambda: |-
      if (isnan(id(tds_1h).state)) return {};
      return id(tds_1h).state * 2.0f;

  # Diagnostics
  - platform: template
    name: "TDS Probe Voltage"
    unit_of_measurement: "V"
    accuracy_decimals: 3
    state_class: measurement
    update_interval: 10s
    entity_category: diagnostic
    lambda: |-
      if (isnan(id(tds_voltage).state)) return {};
      return id(tds_voltage).state;

  # -------------------------------------------------------------
  # BH1750 (GY-302) ambient light -- ADDR floating gives 0x23
  # -------------------------------------------------------------
  - platform: bh1750
    name: "Tank Light Level"
    id: tank_lux
    address: 0x23
    update_interval: 30s
    accuracy_decimals: 0
    filters:
      - filter_out: nan

  # The published water temperature. Fahrenheit, like everything else a
  # human reads here -- the unit is not in the name because there is no
  # other unit it could be in.
  - platform: template
    name: "Water Temperature"
    # id so a two-probe board can !extend the name ("Water Temperature
    # Left"). Nothing here references it; the id changes nothing on its own.
    id: water_temp_f
    unit_of_measurement: "°F"
    device_class: temperature
    state_class: measurement
    accuracy_decimals: 2
    update_interval: 10s
    lambda: |-
      if (isnan(id(water_temp).state)) return {};
      return id(water_temp).state * 9.0f / 5.0f + 32.0f;

# ---------------------------------------------------------------------
# Calibration
# ---------------------------------------------------------------------
# Runtime, from Home Assistant. These used to be substitutions, which
# meant every calibration was a config edit and a reflash -- and a probe
# recalibrated in a bucket at the sink is exactly when you least want a
# build step between you and storing the number.
#
# restore_value so a calibration survives reboots and OTA updates. The
# substitutions remain as the FIRST-BOOT defaults only.
globals:
  - id: cal_tds_k
    type: float
    restore_value: true
    initial_value: '${tds_k_factor}'
  - id: cal_temp_offset_c
    type: float
    restore_value: true
    initial_value: '0.0'

# The lambda-backed numbers below are views onto the globals above, so
# nothing republishes them until update_interval comes round. Every
# set_action ends with a component.update on its own entity, or Home
# Assistant and the device's page snap back to the old value for up to a
# minute after a change that has in fact been stored.
number:
  - platform: template
    name: "Cal TDS K Factor"
    id: cal_tds_k_num
    icon: "mdi:tune-variant"
    entity_category: config
    min_value: 0.10
    max_value: 5.00
    step: 0.01
    unit_of_measurement: "x"
    update_interval: 60s
    lambda: "return id(cal_tds_k);"
    set_action:
      - lambda: id(cal_tds_k) = x;
      - component.update: cal_tds_k_num

  # What the calibration solution is worth. 342 ppm (the 707 uS/cm NaCl
  # standard) and 1000 ppm are the usual bottles; set this to whatever the
  # label says BEFORE pressing Calibrate TDS.
  - platform: template
    name: "Cal TDS Standard"
    id: cal_tds_standard
    icon: "mdi:flask"
    entity_category: config
    optimistic: true
    restore_value: true
    initial_value: 342
    min_value: 1
    max_value: 2000
    step: 1
    unit_of_measurement: "ppm"

  - platform: template
    name: "Cal Temperature Offset"
    id: cal_temp_offset_num
    icon: "mdi:thermometer-plus"
    entity_category: config
    min_value: -5.0
    max_value: 5.0
    step: 0.1
    unit_of_measurement: "\u00b0F"
    update_interval: 60s
    # Stored in Celsius because that is what the probe and the controller
    # use; shown in Fahrenheit because that is what every other temperature
    # in this project is shown in.
    lambda: "return id(cal_temp_offset_c) * 9.0f / 5.0f;"
    set_action:
      - lambda: id(cal_temp_offset_c) = x * 5.0f / 9.0f;
      - component.update: cal_temp_offset_num

button:
  # Put the probe in the standard, wait for the reading to settle, press.
  # Solves for the K factor that makes the CURRENT reading equal the
  # standard, which is the whole of a single-point conductivity calibration.
  - platform: template
    name: "Calibrate TDS"
    id: cal_tds_button
    icon: "mdi:target-variant"
    entity_category: config
    on_press:
      - lambda: |-
          const float shown = id(tds).state;
          const float want = id(cal_tds_standard).state;
          if (std::isnan(shown) || shown < 1.0f || std::isnan(want) || want < 1.0f) {
            ESP_LOGW("cal", "TDS calibration skipped: reading %.1f, standard %.1f", shown, want);
            return;
          }
          // shown was produced with the current k, so the uncalibrated
          // value is shown/k and the k we want is want/(shown/k).
          const float k = id(cal_tds_k) * want / shown;
          if (k < 0.10f || k > 5.00f) {
            ESP_LOGW("cal", "TDS calibration refused: k=%.3f is outside 0.1-5.0, check the probe", k);
            return;
          }
          ESP_LOGI("cal", "TDS calibrated: %.1f ppm -> %.1f ppm, k %.3f -> %.3f",
                   shown, want, id(cal_tds_k), k);
          id(cal_tds_k) = k;
      # Show the result now rather than on the next poll: the new K, and the
      # reading it produces -- which should be the standard the probe is
      # standing in, and is the check that the calibration took.
      - component.update: cal_tds_k_num
      - component.update: tds
