JoshuaSeidel/tank-monitor/packages/light_pod.yaml

# LIGHT POD -- the chip-independent half. Light sensors plus the pH
# board's voltage; no actuators.
#
# Loaded BY a board file, never on its own: the board file owns the chip,
# the esp32: block, the two I2C pins (i2c_sda / i2c_scl) and the pH ADC pin
# (ph_adc_pin),
# and includes this. One copy of the sensor and BLE logic, however many
# boards it has lived on:
#   boards/xiao-esp32s3-light-pod.yaml             Seeed XIAO ESP32-S3
#   boards/sparkfun-esp32c6-pocket-light-pod.yaml  SparkFun Qwiic Pocket ESP32-C6
#
# It measures the light over the 75 gal and reads the pH board's voltage.
# No relay, no heater, no control loop. The light side answers two separate
# questions with two separate parts:
#
#   BH1750  -> lux. How much light, in a real unit. This is the one the
#              controller wants: it feeds the thermal model's light-gain
#              term so the loop can pre-empt the daily light-heat bump
#              instead of chasing it.
#
#   AS7341  -> eight visible bands. WHICH channels are on. Lux cannot
#              answer this: it is photopic, weighted near 555 nm, so it
#              discounts deep red (660) and royal blue (450) hardest --
#              exactly the channels the phase presets command. Move red
#              20% -> 36% and the BH1750 barely twitches.
#
# The two travel by DIFFERENT PATHS, on purpose:
#
#   lux      -> BLE, straight to the controller, peer to peer. No broker,
#               no Home Assistant, no router. It is a control input, so it
#               must not depend on anything that can be down.
#   spectral -> MQTT to Home Assistant (all ten channels), plus the compact
#               blue/red/NIR subset in the same BLE frame as lux.
#   pH volts -> BLE, its own frame, to the controller -- see PH below.
#
# Both also publish to MQTT for history. The BLE path is additive.
#
# ---------------------------------------------------------------------
# PH -- the pod reads it, the controller owns it
# ---------------------------------------------------------------------
# The DFRobot Gravity pH board (SEN0169-V2) sits here, on the pod's own
# supply, instead of on the controller's ADS1115. Two reasons, both about
# the controller's analog side, where the pH channel died on 2026-09-24:
#   - no more millivolt-level wiring through the controller's enclosure;
#   - the electrode no longer shares a ground with the TDS probe and the
#     heater relays, which is a known way to get a wandering pH.
#
# The pod sends the board's VOLTAGE, not a pH. The controller keeps
# packages/ph.yaml unchanged: the two-point calibration and its capture
# buttons, the temperature compensation (the pod has no water temperature;
# the controller does), and the "Water pH" entity everything else reads.
# A calibration is still per-converter, though: volts read through this
# board's ADC are not the volts the controller's ADS1115 read, so
# RECALIBRATE after the move.
#
# The Gravity board buffers the electrode, so the ADC sees a low-impedance
# op-amp output between about 1 and 2 V across pH 4-10 -- the ESP32 ADC's
# most linear stretch. Two-point calibration through this same ADC cancels
# its offset and gain error; what is left is a few mV, roughly 0.02-0.05
# pH, inside what the probe itself can tell apart.
#
# ---------------------------------------------------------------------
# WHAT THE SPECTRAL SIDE IS NOT
# ---------------------------------------------------------------------
# Not PAR. The counts are uncalibrated ADC values, not micromoles, and the
# Seneye was returned from this project for exactly that failure -- a
# continuous reading nobody could check, believed for months, wrong the
# whole time. Valid use is DIFFERENTIAL only: this week against last week,
# same sensor, same place, same gain.
#
# The AS7341 must never feed tank_lux. The control loop normalises against
# full_scale_lux and tests light_on_lux, both in real lux. That is what the
# BH1750 on this same bus is for.
#
# ---------------------------------------------------------------------
# MOUNTING -- the readings are worthless if this moves
# ---------------------------------------------------------------------
# Everything the AS7341 produces is relative, so the geometry IS the
# calibration. Fix it permanently. Face it UP at the fixture, never down at
# the water (that measures reflections off a moving surface). Put no glass
# in the light path: a lid BENEATH the sensor is a splash shield, but a lid
# ABOVE it is condensation and mineral film -- a slowly varying attenuation
# indistinguishable from the lamp dimming. Shield the window side; the
# 09:00-16:00 photoperiod runs straight through the brightest part of the
# day.
#
# ---------------------------------------------------------------------
# WHAT THIS PACKAGE OWES AND IS OWED
# ---------------------------------------------------------------------
# Owed by the board file: i2c_sda, i2c_scl, ph_adc_pin and the esp32:
# block. ph_adc_pin must be an ADC1 pin that is NOT a strapping pin: the pH
# board idles near 1.5 V, which would hold a strapping pin at an undefined
# level during boot.
# Owed to nobody: packages/base.yaml supplies wifi, MQTT, OTA, the web
# server and the clock. Never pair this with control.yaml, sensors.yaml
# or ph.yaml: there is no probe, heater or relay here for them to bind to.
#
# Both sensors share one bus with no address conflict: BH1750 at 0x23 (ADDR
# floating) and AS7341 at 0x39 (fixed). Leave the BH1750's ADDR pin alone --
# the 0x5C jumper is only needed when two of them share a bus, and that
# splice is what shorted the 3V3 rail on the last attempt.

substitutions:
  # 10 kHz, the same decision as both controllers. Short leads here do not
  # need it, but it costs nothing on a board reading two sensors a minute
  # and it leaves headroom if a sensor ever ends up on a longer lead.
  i2c_freq: "10kHz"

  # ---- The controller's BLE MAC -- you must set this ----
  # Read it from the controller, do NOT compute it. It publishes the value
  # as sensor.tank_monitor_75_gallon_controller_ble_mac, and it is also in
  # its boot log. On an ESP32-S3 the BLE MAC is the WiFi MAC + 2 in the last
  # octet, but that relationship is not a promise -- read the real one.
  controller_mac: "SET-ME-FROM-THE-CONTROLLER"

  # Nordic UART Service UUIDs, matching packages/ble_link_v3.yaml. The
  # sensor characteristic is 0x...04, deliberately NOT the command
  # characteristic (0x...02) the panel writes setpoints to -- sensor ingress
  # and "move the tank's target temperature" do not share a channel.
  link_service:   "6e400001-b5a3-f393-e0a9-e50e24dcca9e"
  link_sens_char: "6e400004-b5a3-f393-e0a9-e50e24dcca9e"

  # How often lux (and the pH voltage) is pushed to the controller. The thermal model works on
  # 15-minute actuator windows, so a minute is already far finer than it can
  # act on. Each push is a connect / write / disconnect, so this also sets
  # how often the controller briefly holds a second BLE connection.
  lux_push_interval: "60s"

  # What "I2C Devices" expects to answer on the bus: "addr label, ...".
  i2c_expect: "0x23 BH1750, 0x39 AS7341"

  lux_update: "30s"

  # The AS7341 and everything derived from it live in packages/spectral.yaml,
  # shared with boards/allinone-freenove.yaml; this is the bus it sits on.
  spectral_i2c: bus_a

# ESPHome's default MQTT unique_id generator is "legacy": "ESP" + component
# type + object_id, with NO device name and no MAC in it. Two boards with a
# same-named entity therefore generate byte-identical unique_ids, and Home
# Assistant silently refuses the second one. This board publishes a "Tank
# Light Level" exactly like the 12 gal controller does, so without this it
# would collide on day one.
#
# In the BOARD FILE, not the wrapper -- putting load-critical config in the
# wrapper has silently failed four times in this project.
mqtt:
  discovery_unique_id_generator: mac

# I2C bus autopsy, run BEFORE the driver claims the pins (bus priority is
# 1000; this is 1001) -- the same check the 75 gal controller runs. The scan
# cannot tell a wire that reaches a powered sensor from one that reaches
# nothing, because it turns on the chip's own pull-ups first. This asks each
# line two questions with those pull-ups OFF:
#
#   ext-pullup  With only the chip's ~45k pull-DOWN on, a line reads 0
#               unless a sensor's own pull-up (to its powered VCC) lifts
#               it. "yes" = the wire reaches a sensor that has power.
#               "NO" = open wire, wrong pin, or no power at the sensor.
#   drives-low  Driven low and read back. Anything but 0 is a line tied
#               hard to 3V3 -- a wire on the wrong pin.
#
# Reported through "I2C Devices" below, so it reaches Home Assistant with no
# serial cable. List form on purpose: a mapping-form on_boot in a package
# can be dropped silently when packages merge.
esphome:
  on_boot:
    - priority: 1001
      then:
        - lambda: |-
            const gpio_num_t pins[2] = {(gpio_num_t) ${i2c_sda}, (gpio_num_t) ${i2c_scl}};
            const char *names[2] = {"SDA", "SCL"};
            std::string r;
            for (int i = 0; i < 2; i++) {
              gpio_config_t c{};
              c.pin_bit_mask = 1ULL << pins[i];
              c.mode = GPIO_MODE_INPUT;
              c.pull_up_en = GPIO_PULLUP_DISABLE;
              c.pull_down_en = GPIO_PULLDOWN_ENABLE;
              c.intr_type = GPIO_INTR_DISABLE;
              gpio_config(&c);
              delayMicroseconds(200);
              const int ext = gpio_get_level(pins[i]);
              c.mode = GPIO_MODE_INPUT_OUTPUT_OD;
              c.pull_up_en = GPIO_PULLUP_ENABLE;
              c.pull_down_en = GPIO_PULLDOWN_DISABLE;
              gpio_config(&c);
              gpio_set_level(pins[i], 0);
              delayMicroseconds(200);
              const int low = gpio_get_level(pins[i]);
              gpio_set_level(pins[i], 1);
              delayMicroseconds(200);
              const int high = gpio_get_level(pins[i]);
              char b[64];
              snprintf(b, sizeof(b), "%s%s ext-pullup %s, drives-low %s, releases %s",
                       i ? "; " : "", names[i], ext ? "yes" : "NO",
                       low == 0 ? "yes" : "NO", high ? "yes" : "NO");
              r += b;
            }
            id(i2c_autopsy) = r;
            ESP_LOGI("i2c", "autopsy: %s", r.c_str());

globals:
  - id: i2c_autopsy
    type: std::string
    restore_value: false
    initial_value: '""'

text_sensor:
  # Which expected devices answer, once a minute. The sensor components only
  # probe at boot and then go quiet, so without this a missing sensor is
  # just "unknown" forever. When something is missing it also sweeps every
  # address (a sensor at the WRONG address shows up by where it is) and
  # appends the boot autopsy above. After fixing a wire this line goes
  # right within a minute; the readings come back after a restart.
  - platform: template
    name: "I2C Devices"
    id: i2c_devices
    icon: "mdi:transit-connection-variant"
    entity_category: diagnostic
    update_interval: 60s
    lambda: |-
      static const char *spec = "${i2c_expect}";
      std::string out;
      bool all_ok = true;
      bool stuck = false;
      const char *p = spec;
      while (*p) {
        while (*p == ' ' || *p == ',') p++;
        if (!*p) break;
        char *end = nullptr;
        const uint8_t addr = (uint8_t) strtol(p, &end, 0);
        p = end;
        while (*p == ' ') p++;
        std::string what;
        while (*p && *p != ',') what += *p++;
        while (!what.empty() && what.back() == ' ') what.pop_back();
        App.feed_wdt();
        const auto err = id(bus_a).write_readv(addr, nullptr, 0, nullptr, 0);
        if (!out.empty()) out += ", ";
        out += what;
        switch (err) {
          case i2c::ERROR_OK:               out += " ok"; break;
          case i2c::ERROR_NOT_ACKNOWLEDGED: out += " no ack"; all_ok = false; break;
          case i2c::ERROR_TIMEOUT:          out += " TIMEOUT"; all_ok = false; stuck = true; break;
          default:                          out += " error"; all_ok = false; break;
        }
      }
      // A TIMEOUT is not a missing device, it is a HUNG BUS: something is
      // holding SDA or SCL. Every further transaction waits out the same
      // ~100 ms timeout, so a full sweep would block the loop for >10 s and
      // the task watchdog reboots the board -- a boot loop that takes the
      // device off the network. Report it and stop.
      if (stuck) {
        out += "; BUS STUCK: a device or wire is holding SDA/SCL -- sweep skipped";
        if (!id(i2c_autopsy).empty()) out += "; at boot: " + id(i2c_autopsy);
        return out;
      }
      if (!all_ok) {
        std::string found;
        for (uint8_t a = 0x08; a < 0x78; a++) {
          App.feed_wdt();
          const auto e = id(bus_a).write_readv(a, nullptr, 0, nullptr, 0);
          if (e == i2c::ERROR_TIMEOUT) { found += found.empty() ? "(bus hung mid-sweep)" : " (bus hung mid-sweep)"; break; }
          if (e != i2c::ERROR_OK) continue;
          char b[8];
          snprintf(b, sizeof(b), "%s0x%02X", found.empty() ? "" : " ", a);
          found += b;
        }
        out += found.empty() ? "; bus sweep: nothing" : "; bus sweep found: " + found;
        if (!id(i2c_autopsy).empty()) out += "; at boot: " + id(i2c_autopsy);
      }
      return out;

i2c:
  sda: ${i2c_sda}
  scl: ${i2c_scl}
  frequency: ${i2c_freq}
  id: bus_a
  scan: true

# BLE client, to push lux at the controller. WiFi + BLE is the supported
# pair on this silicon; ESP-NOW is deliberately absent, because WiFi +
# ESP-NOW + BLE together is the combination that cost this project a link
# and then a web server.
esp32_ble_tracker:
  scan_parameters:
    # Passive and unhurried. This board only ever talks to one known MAC,
    # so there is nothing to discover and no reason to hold the radio.
    interval: 1100ms
    window: 300ms
    active: false

ble_client:
  - mac_address: ${controller_mac}
    id: ctrl_link
    on_connect:
      then:
        # Let the GATT discovery settle before writing. Same shape as the
        # Chihiros bridge: connect, do one thing, disconnect.
        - delay: 500ms
        # The pod connects when EITHER reading is valid, so each frame is
        # guarded on its own: a missing BH1750 must not send "L,0" (a lux
        # of zero is a reading, not silence), and a missing pH board must
        # not send anything at all.
        - if:
            condition:
              lambda: 'return !isnan(id(pod_lux).state);'
            then:
              - ble_client.ble_write:
                  id: ctrl_link
                  service_uuid: ${link_service}
                  characteristic_uuid: ${link_sens_char}
                  # FRAME: L,<lux>,<blue%>,<red%>,<nir/1000>  -- 5 fields, <= 19 bytes.
                  #
                  # The size is not an accident. A BLE write carries 20 bytes of
                  # payload until an MTU negotiation succeeds, and while ESPHome
                  # does request a larger one on connect, the granted size is
                  # whatever both ends agree -- not a promise. A frame that fits
                  # in the default works no matter how that negotiation lands.
                  #
                  # Which is why green is NOT sent: the three shares are computed
                  # over all eight bands and sum to 100, so the controller
                  # reconstructs it as 100 - blue - red. Blue and red are the ends
                  # of the spectrum and the channels actually being tuned; green
                  # is the one that can be inferred.
                  #
                  # -1 means "spectral not ready yet" -- the AS7341 has a slower
                  # update than the BH1750, and lux must not wait on it.
                  value: !lambda |-
                    const float lux = id(pod_lux).state;
                    const float b   = id(sp_share_blue).state;
                    const float r   = id(sp_share_red).state;
                    const float n   = id(sp_nir_ratio).state;
                    int L = isnan(lux) ? 0 : (int) lroundf(lux);
                    if (L < 0) L = 0;
                    if (L > 65535) L = 65535;
                    const int B = isnan(b) ? -1 : (int) lroundf(b);
                    const int R = isnan(r) ? -1 : (int) lroundf(r);
                    int N = isnan(n) ? -1 : (int) lroundf(n * 1000.0f);
                    if (N > 999) N = 999;
                    char buf[24];
                    const int len = snprintf(buf, sizeof(buf), "L,%d,%d,%d,%d", L, B, R, N);
                    return std::vector<uint8_t>(buf, buf + len);
        - delay: 200ms
        - if:
            condition:
              lambda: 'return !isnan(id(pod_ph_v).state);'
            then:
              - ble_client.ble_write:
                  id: ctrl_link
                  service_uuid: ${link_service}
                  characteristic_uuid: ${link_sens_char}
                  # FRAME: P,<volts x 10000>   e.g. "P,14803" = 1.4803 V
                  #
                  # Its own frame rather than a sixth field on L: L already
                  # runs to 19 bytes against a 20-byte write. An integer in
                  # tenths of a millivolt keeps the ADC's resolution (the
                  # electrode moves ~170 mV per pH unit, so 0.1 mV is
                  # 0.0006 pH) without a float parser on the far end.
                  value: !lambda |-
                    int P = (int) lroundf(id(pod_ph_v).state * 10000.0f);
                    if (P < 0) P = 0;
                    if (P > 33000) P = 33000;
                    char buf[12];
                    const int len = snprintf(buf, sizeof(buf), "P,%d", P);
                    return std::vector<uint8_t>(buf, buf + len);
              - delay: 200ms
        # Non-persistent by design. Holding the link open would keep the
        # controller at two BLE connections permanently and give the panel
        # a radio to share all day; this way the overlap is a second a
        # minute. The controller's staleness guard covers the gaps.
        - switch.turn_off: ctrl_conn
    on_disconnect:
      then:
        - logger.log:
            format: "controller link: disconnected"
            level: DEBUG

switch:
  - platform: ble_client
    ble_client_id: ctrl_link
    id: ctrl_conn
    internal: true
    restore_mode: ALWAYS_OFF

interval:
  - interval: ${lux_push_interval}
    then:
      # Never push a NaN. A missing reading must reach the controller as
      # silence, so its staleness guard can time out and drop the light term
      # (or blank the pH) -- not as a number that happens to parse. Connect
      # if there is anything worth sending; on_connect sends only what is.
      - if:
          condition:
            lambda: 'return !isnan(id(pod_lux).state) || !isnan(id(pod_ph_v).state);'
          then:
            - switch.turn_on: ctrl_conn

sensor:
  # -------------------------------------------------------------
  # pH board voltage -- the DFRobot Gravity SEN0169-V2 output.
  # Sent to the controller, which does the pH maths; see PH above.
  # Published here as well so a dead BLE link and a dead probe look
  # different from Home Assistant: this moves and "Water pH" does not
  # means the link, both flat means the probe.
  # -------------------------------------------------------------
  - platform: adc
    pin: ${ph_adc_pin}
    name: "pH Board Voltage"
    id: pod_ph_v
    unit_of_measurement: "V"
    accuracy_decimals: 4
    entity_category: diagnostic
    attenuation: 12db
    # 16 conversions averaged per reading, then the median of the last
    # 30 s: the radio's transmit bursts land on the supply as short spikes,
    # and between the two they cost nothing on a value that moves over
    # hours. One published value every 30 s, two per BLE push.
    samples: 16
    update_interval: 1s
    filters:
      - median:
          window_size: 30
          send_every: 30
          send_first_at: 5

  # -------------------------------------------------------------
  # BH1750 (GY-302) -- real lux, ADDR floating gives 0x23.
  # This is the one the controller consumes.
  # -------------------------------------------------------------
  - platform: bh1750
    name: "Tank Light Level"
    id: pod_lux
    address: 0x23
    update_interval: ${lux_update}
    accuracy_decimals: 0
    filters:
      - filter_out: nan

# The AS7341, its byte-order fix, the shares, NIR ratio and saturation flag.
# Shared with boards/allinone-freenove.yaml so both boards run the same code.
packages:
  spectral: !include spectral.yaml
